basilfx/TRADFRI-Hacking/products/ICPSLC24-10NA/README.md

# ICPSLC24-10NA
LED output controller/dimmer

## Details

* Potted: no

The output appears to be measured by the module somehow.

## Teardown

* [Images](images)
* [Schematics](schematics)

## Pinout

### Module (unverified)
* PA0: K1 (Reset key)
* PA1: Goes to ZD1, through R9 and then to OUT+, possibly output measuring?
* PB13: Pulls down the FET Gate
* PF0: Pin 2 on header
* PF1: Pin 3 on header
