basilfx/TRADFRI-Hacking/products/LED1536G5/README.md

# LED1536G5
TRÅDFRI bulb E12/E14, white spectrum, globe, opal, 400 lm.

## Details

* Socket: E14
* Potted: likely
