basilfx/TRADFRI-Hacking/products/LED1537R6/README.md

# LED1537R6
TRÅDFRI bulb GU10, white spectrum, 400 lm.

## Details

* Socket: GU10
* Potted: yes

## Teardown
The potting material can be easily removed. It does not stick and will crumble
in smaller peaces once you remove it.

* [Images](images)

## Pinouts
* 1: Common (+ max 28.4V @ 100%)
* 2: Warm leds (-)
* 3: Cold leds (-)
