basilfx/TRADFRI-Hacking/products/LED1545G12/README.md

# LED1545G12
TRÅDFRI bulb E26/E27, white spectrum, globe, opal, 980 lm.

## Details:

* Socket: E27
* Potted: likely
