basilfx/TRADFRI-Hacking/products/LED1546G12/README.md

# LED1546G12
TRADFRI bulb E26/E27, white spectrum, globe, clear, 950 lm.

## Details

* Socket: E27
* Potted: likely
