basilfx/TRADFRI-Hacking/products/LED1622G12/README.md

# LED1622G12
TRÅDFRI bulb E26, white, globe, opal, 1000 lm.

## Details

* Socket: E27
* Potted: likely
