basilfx/TRADFRI-Hacking/products/LED1623G12/README.md

# LED1623G12
TRÅDFRI bulb E27, white, globe, opal, 1000 lm.

## Details

* Socket: E27
* Potted: likely
