basilfx/TRADFRI-Hacking/products/LED1624G9/README.md

# LED1624G9
TRÅDFRI bulb E12/E14/E26/E27, color/white spectum, globe, opal, 600 lm.

## Details

* Socket: E27
* Potted: likely
