basilfx/TRADFRI-Hacking/products/LED1650R5/README.md

# LED1650R5
TRÅDFRI bulb GU10, white, 400 lm

## Details

* Socket: GU10
* Potted: no
* TRÅDFRI Module: ICC-1

## Teardown
Use a small flat screw driver to lift up the plastic lens.

* [Images](products/LED1650R5/images)

## Pinout

### Module

* PA1 -> unused (but soldered)
* PB13 -> LED driver

## Power consumption
Measured using a Voltcraft 3000 energy monitor.

| Brightness | Power (W) | Cos φ |
|---|---|---|
| 100% | 6.0 | 0.80  |
| 50% | 1.6 | 0.62  |
| 10% | 0.7 | 0.40  |
| Off | 0.0 | 1.00  |
