basilfx/TRADFRI-Hacking/contrib/pcbs/devboard/README.md

# Devboard
Development board to house an ICC-A or ICC-A-1 TRÅDFRI module.

## Known issues
* This board has a non-optimal design for wireless usage. However, the main
  goal of this board is to provide easier pin access.

## Pictures
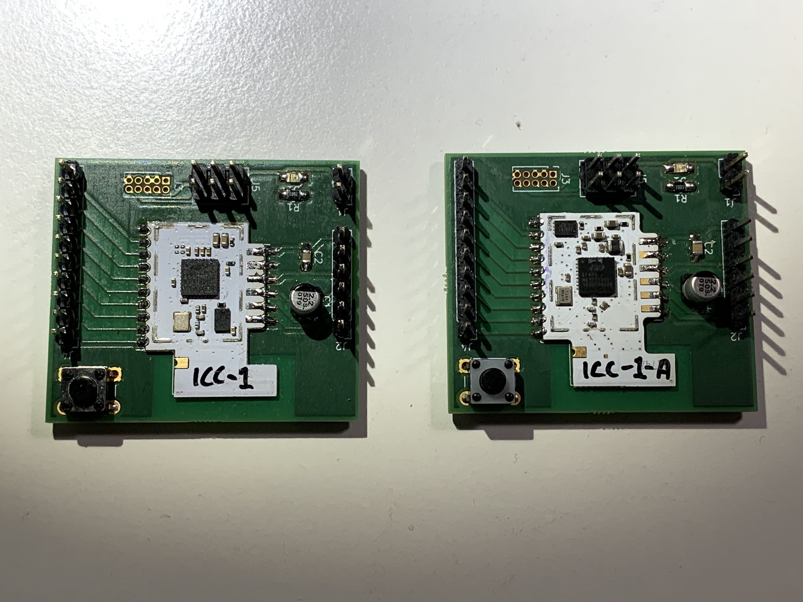
[picture p6: contrib/pcbs/devboard/images/Devboard.jpg]
Assembled board
[](images/Devboard.jpg)

## Board
Top layer
Bottom layer

## Schema
You can find the schema [here](Devboard.pdf).
