basilfx/TRADFRI-Hacking/contrib/pcbs/isolator/README.md

# Isolator
Tiny board to isolate UART RX/TX from target board.

## Pictures
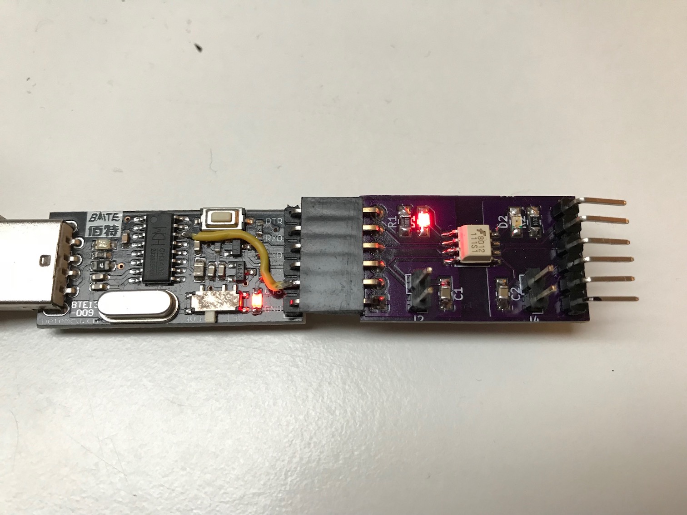
[picture p7: contrib/pcbs/isolator/images/Isolator.jpg]
Assembled board
[](images/Isolator.jpg)

## Board
Top layer
Bottom layer

## Schema
You can find the schema [here](Isolator.pdf).
