basilfx/TRADFRI-Hacking/firmwares/riot-os/spi_flash_dump/README.md

# SPI Flash Dump
Pre-compiled firmware to dump the contents of the SPI NOR Flash chip.

## Source
https://github.com/basilfx/RIOT-applications/tree/master/spi_flash_dump

## Compilation
Ensure that you have a copy of RIOT-OS cloned. 

To compile, run `RIOTBASE=path/to/riot-os BOARD=ikea-tradfri make`.
