basilfx/TRADFRI-Hacking/firmwares/riot-os/default/README.md

# Default
Pre-compiled firmware of RIOT-OS' default application

## Source
https://github.com/RIOT-OS/RIOT/tree/master/examples/default

## Compilation
Ensure that you have a copy of RIOT-OS cloned. 

To compile, run `RIOTBASE=path/to/riot-os BOARD=ikea-tradfri make`.
