basilfx/TRADFRI-Hacking/firmwares/riot-os/spi_flash_identify/README.md

# SPI Flash Identify
Pre-compiled firmware to identify the SPI NOR Flash chip.

## Source
https://github.com/basilfx/RIOT-applications/tree/master/spi_flash_identify

## Compilation
Ensure that you have a copy of RIOT-OS cloned. 

To compile, run `RIOTBASE=path/to/riot-os BOARD=ikea-tradfri make`.
