basilfx/TRADFRI-Hacking/docs/firmware_reversing/images/screenshot_1.png

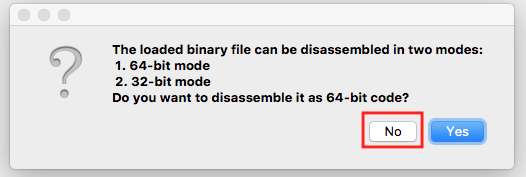
docs/firmware_reversing/images/screenshot_1.png
