basilfx/TRADFRI-Hacking/docs/firmware_reversing/images/screenshot_2.png

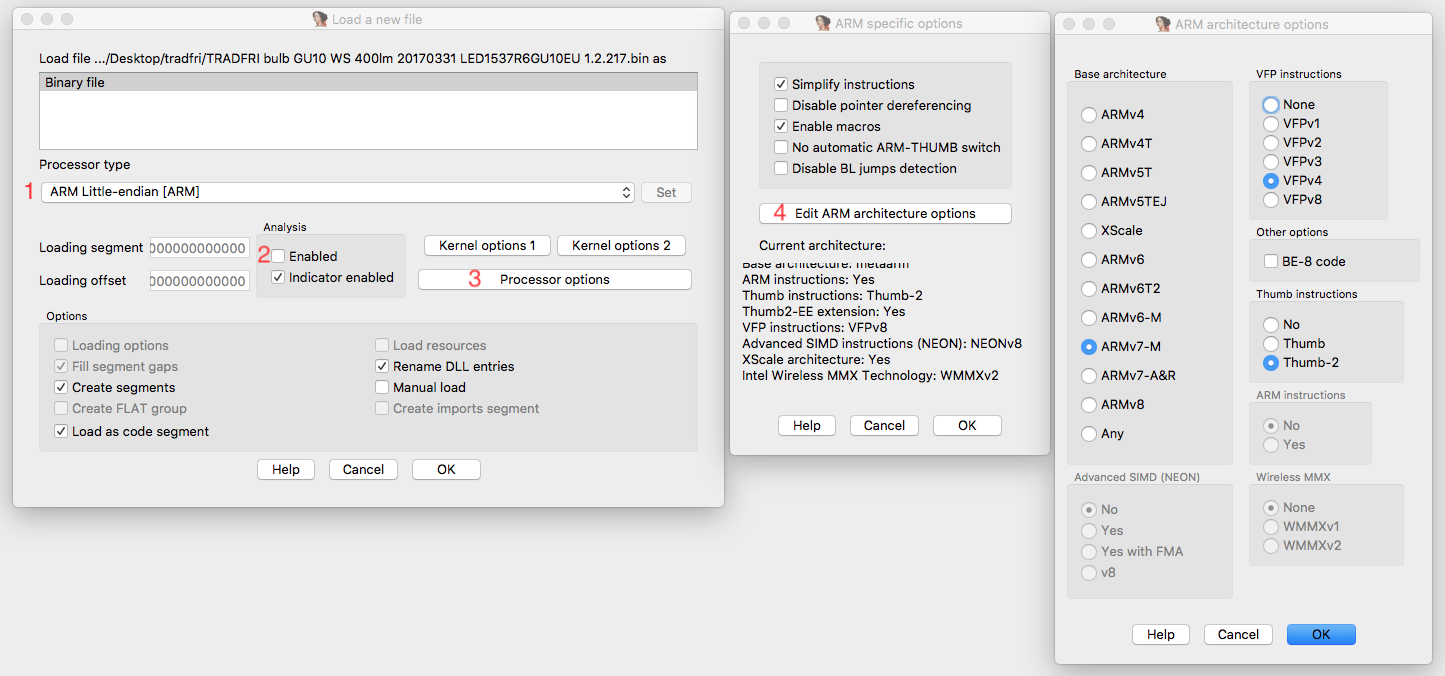
docs/firmware_reversing/images/screenshot_2.png
