basilfx/TRADFRI-Hacking/docs/firmware_reversing/images/screenshot_3.png

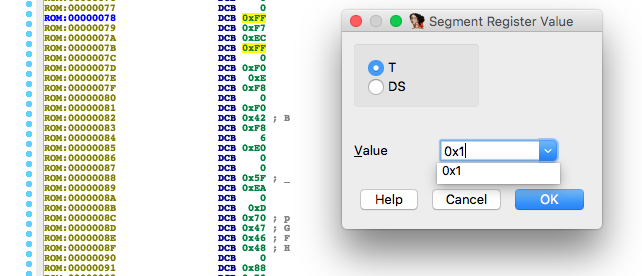
docs/firmware_reversing/images/screenshot_3.png
