basilfx/TRADFRI-Hacking/docs/firmware_reversing/images/screenshot_5.png

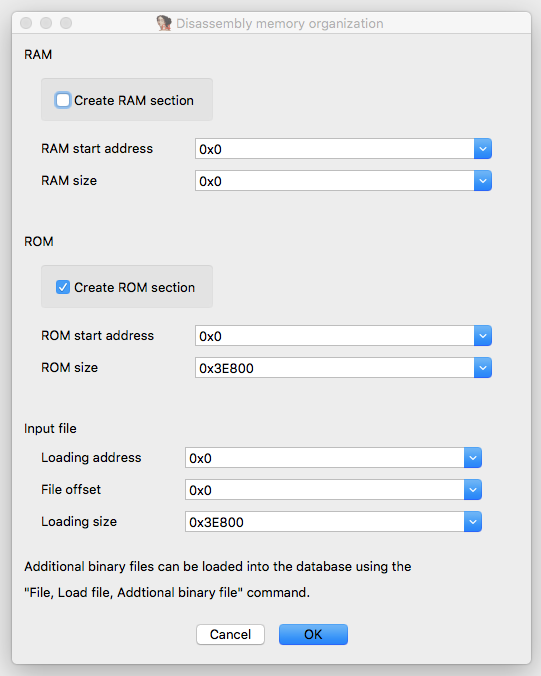
docs/firmware_reversing/images/screenshot_5.png
