basilfx/TRADFRI-Hacking/docs/working_safely/images/led.jpg

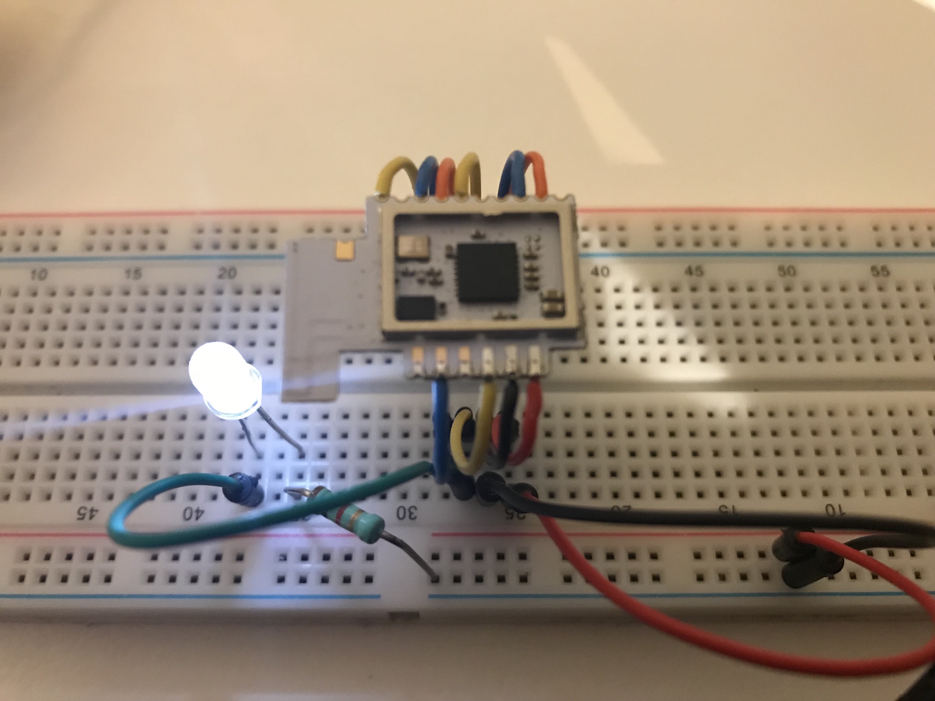
docs/working_safely/images/led.jpg
