basilfx/TRADFRI-Hacking/products/E1526/images/case.jpg

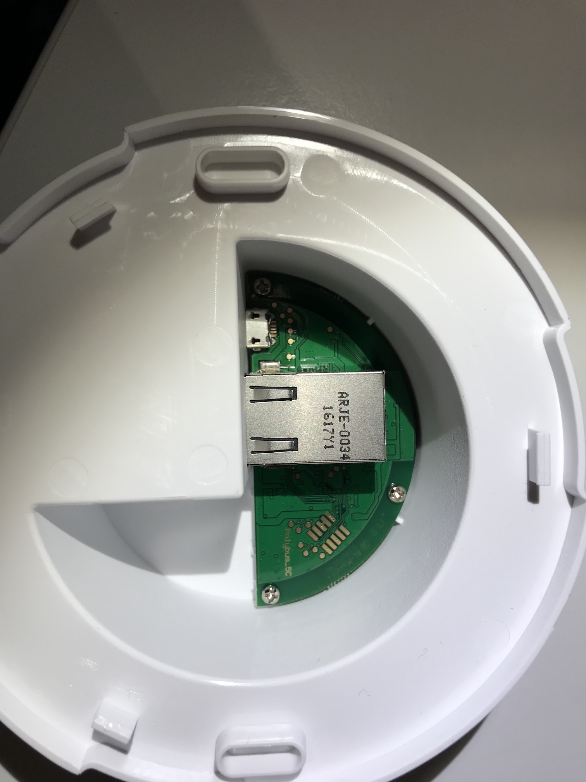
products/E1526/images/case.jpg
