basilfx/TRADFRI-Hacking/products/E1526/images/pcb.jpg

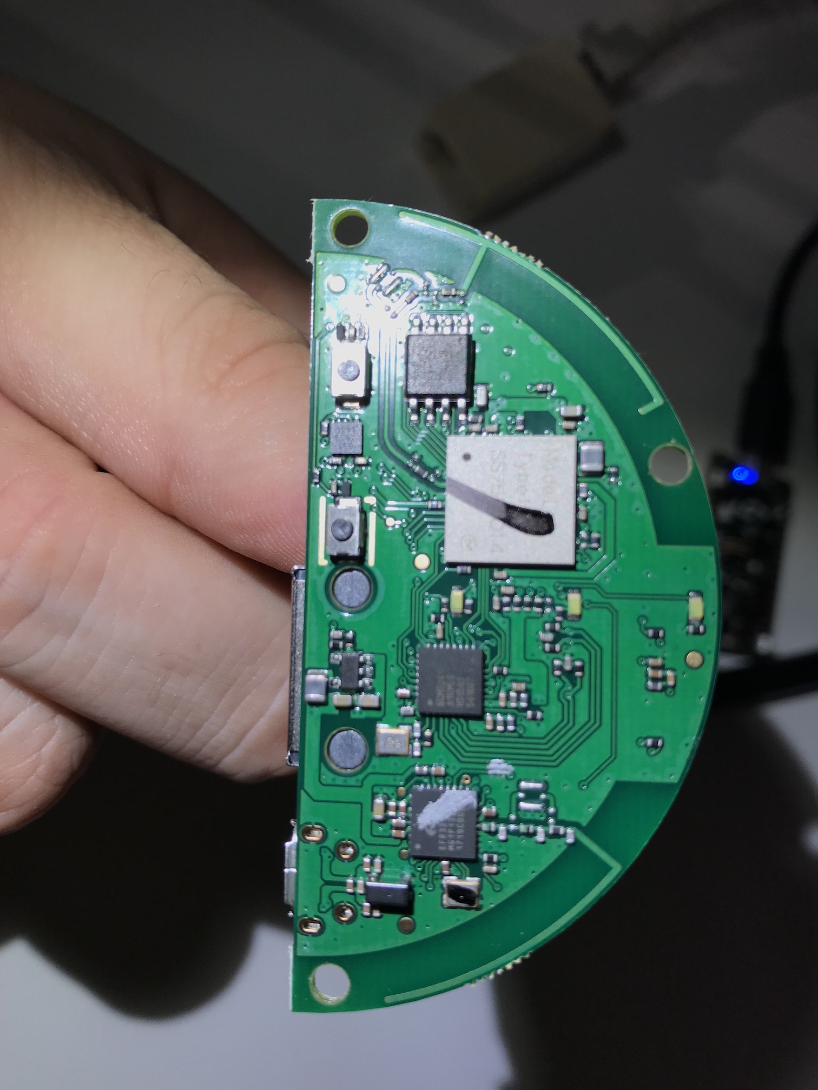
products/E1526/images/pcb.jpg
