basilfx/TRADFRI-Hacking/products/E1745/images/back.jpg

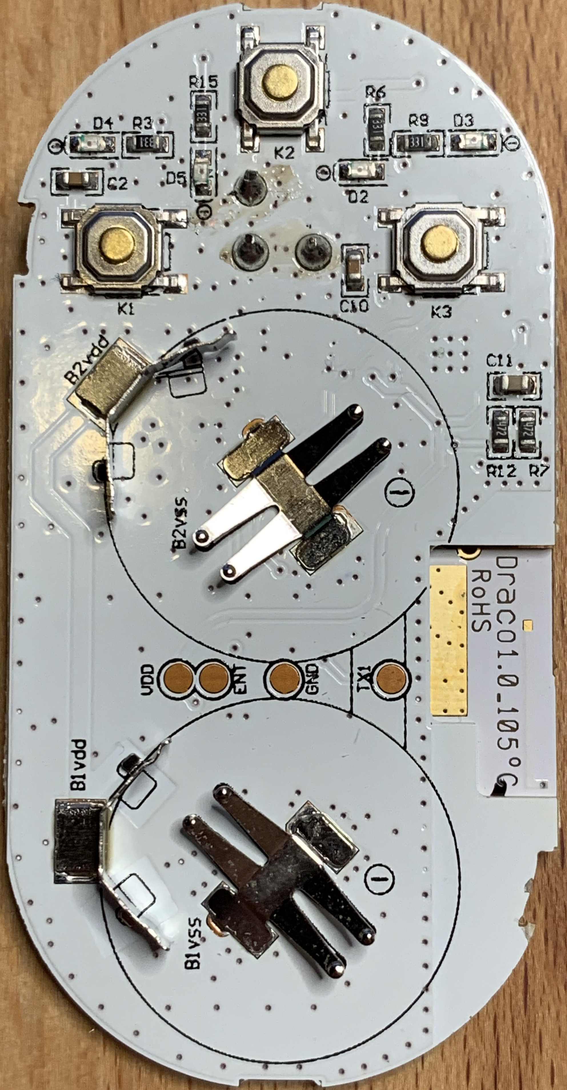
products/E1745/images/back.jpg
