basilfx/TRADFRI-Hacking/products/E1745/images/front.jpg

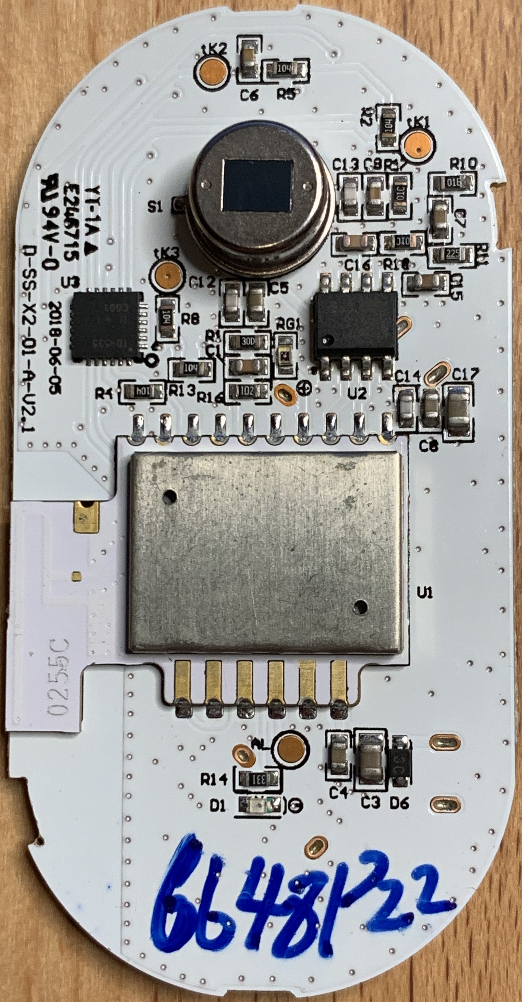
products/E1745/images/front.jpg
