basilfx/TRADFRI-Hacking/products/E1812/images/back.jpg

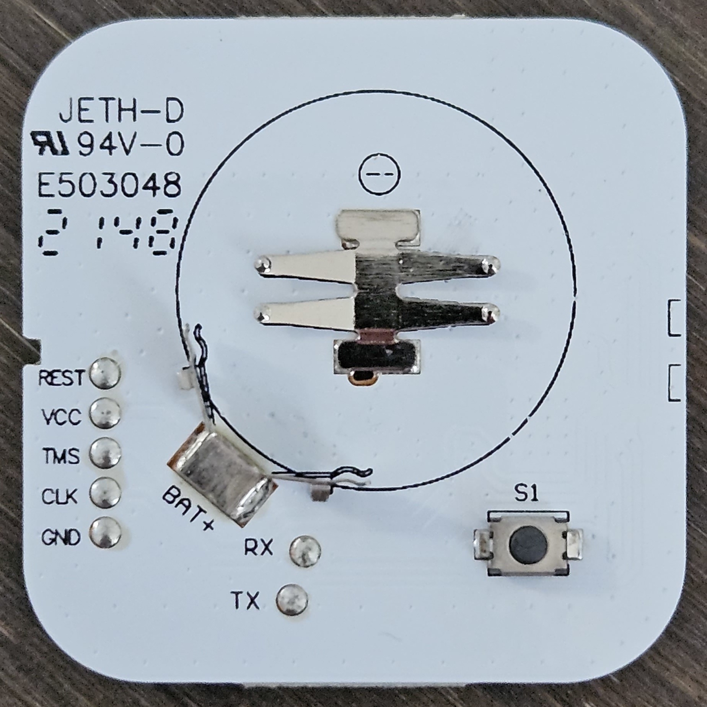
products/E1812/images/back.jpg
