basilfx/TRADFRI-Hacking/products/E1812/images/front.jpg

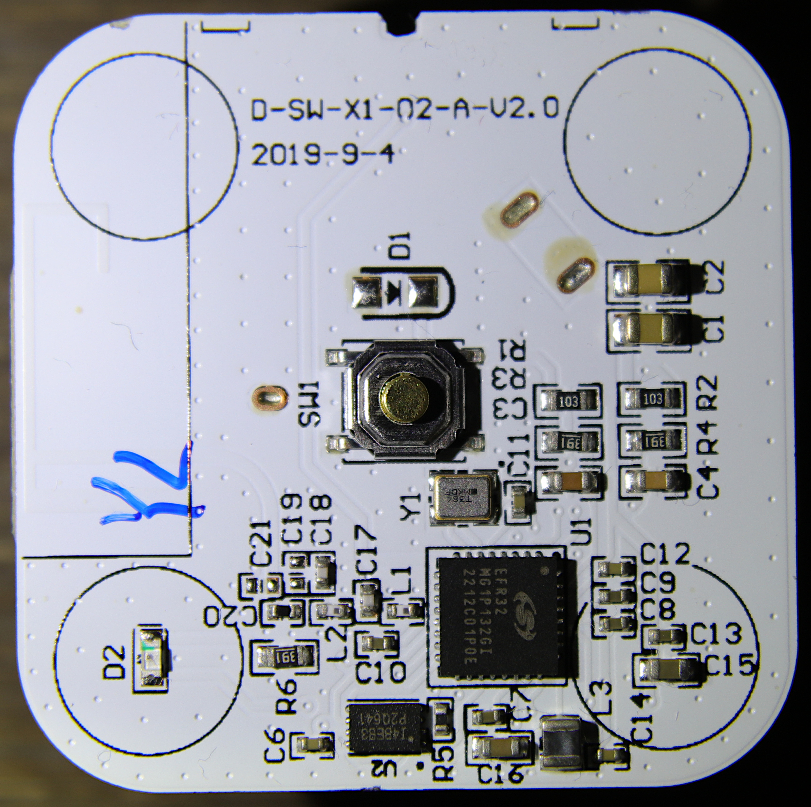
products/E1812/images/front.jpg
