basilfx/TRADFRI-Hacking/products/E1836/images/IMG_1090.jpeg

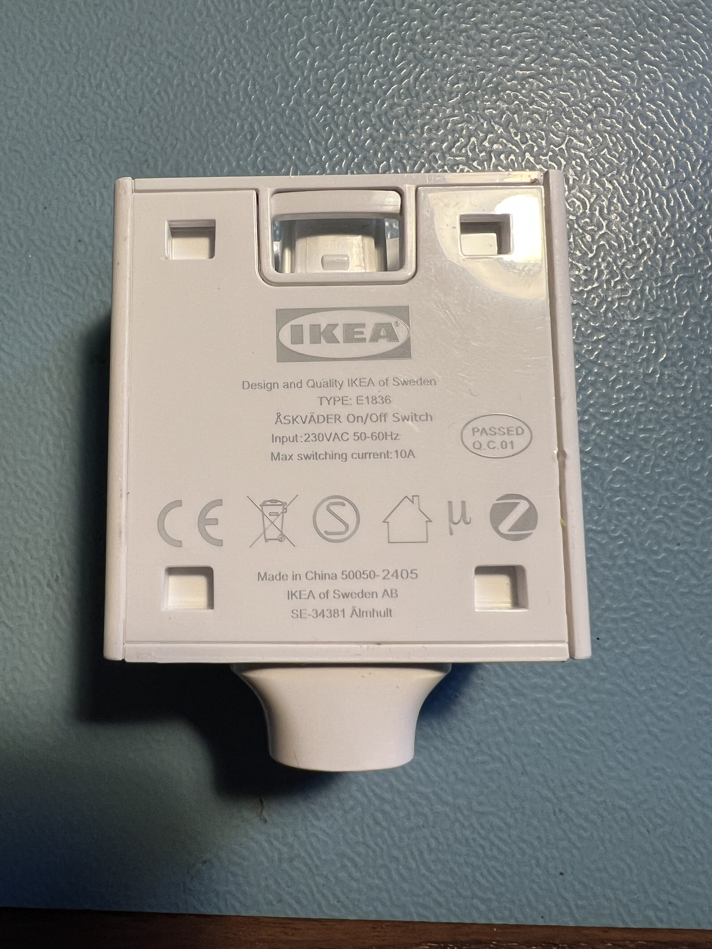
products/E1836/images/IMG_1090.jpeg
