basilfx/TRADFRI-Hacking/products/E1836/images/IMG_1091.jpeg

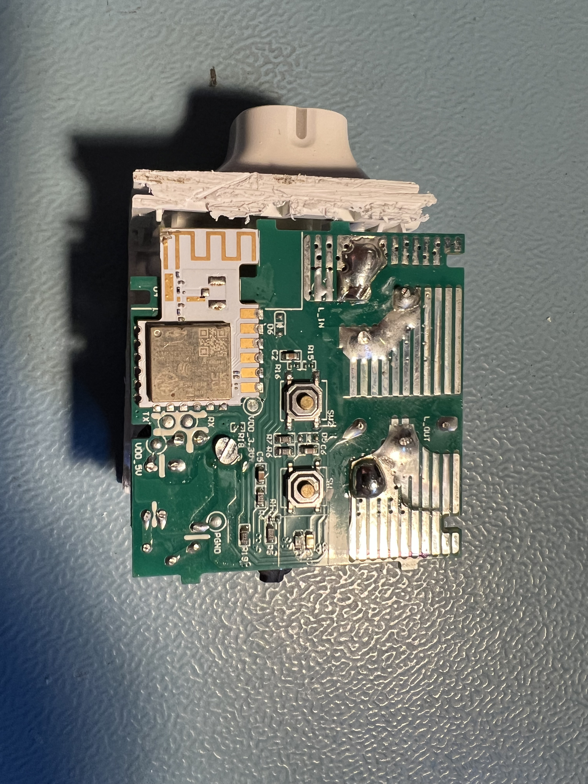
products/E1836/images/IMG_1091.jpeg
