basilfx/TRADFRI-Hacking/products/E1836/images/IMG_1092.jpeg

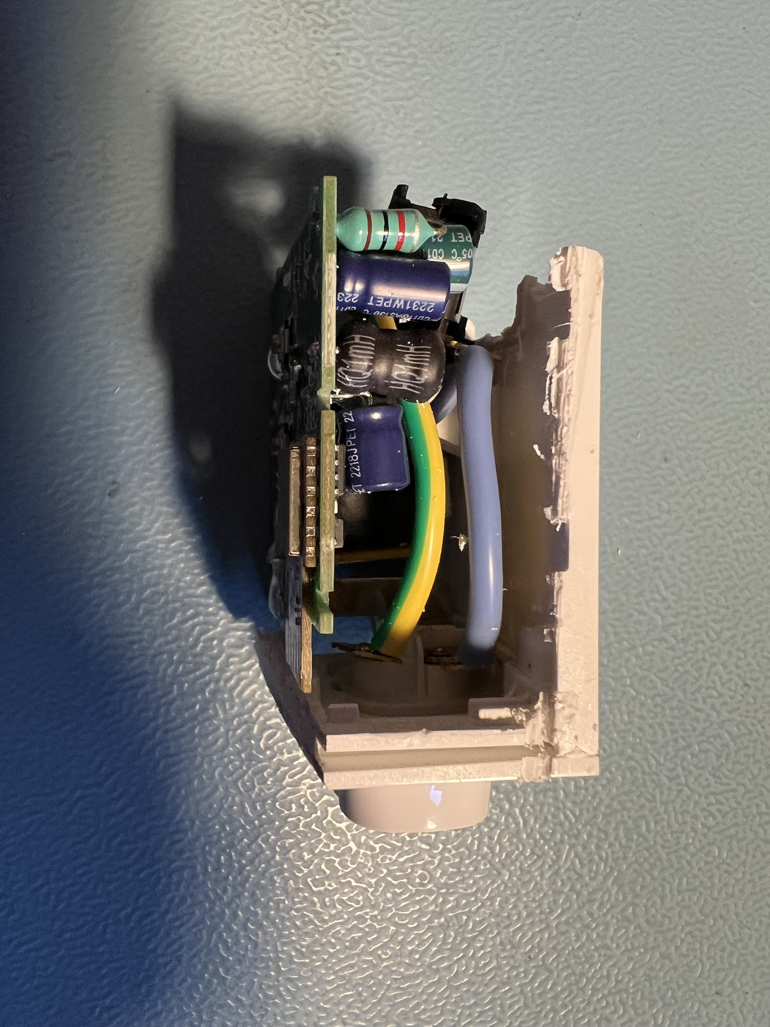
products/E1836/images/IMG_1092.jpeg
