basilfx/TRADFRI-Hacking/products/E1836/images/IMG_1093.jpeg

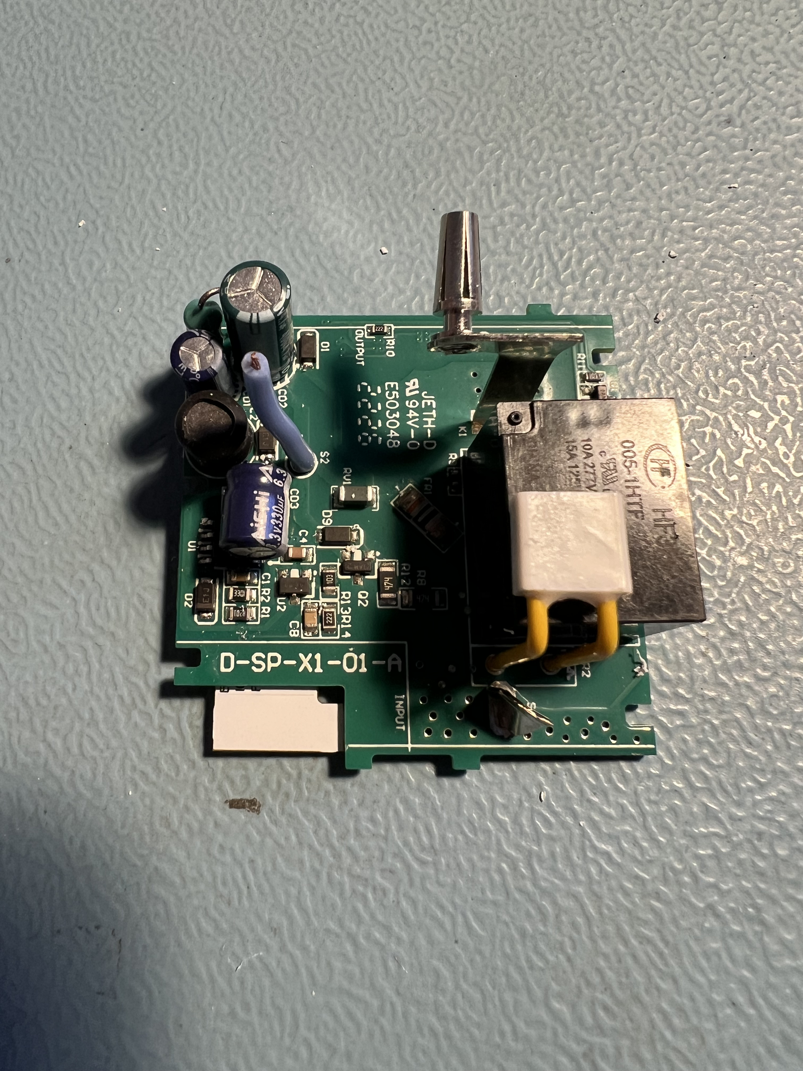
products/E1836/images/IMG_1093.jpeg
