basilfx/TRADFRI-Hacking/products/E2013/images/pcb-back.jpg

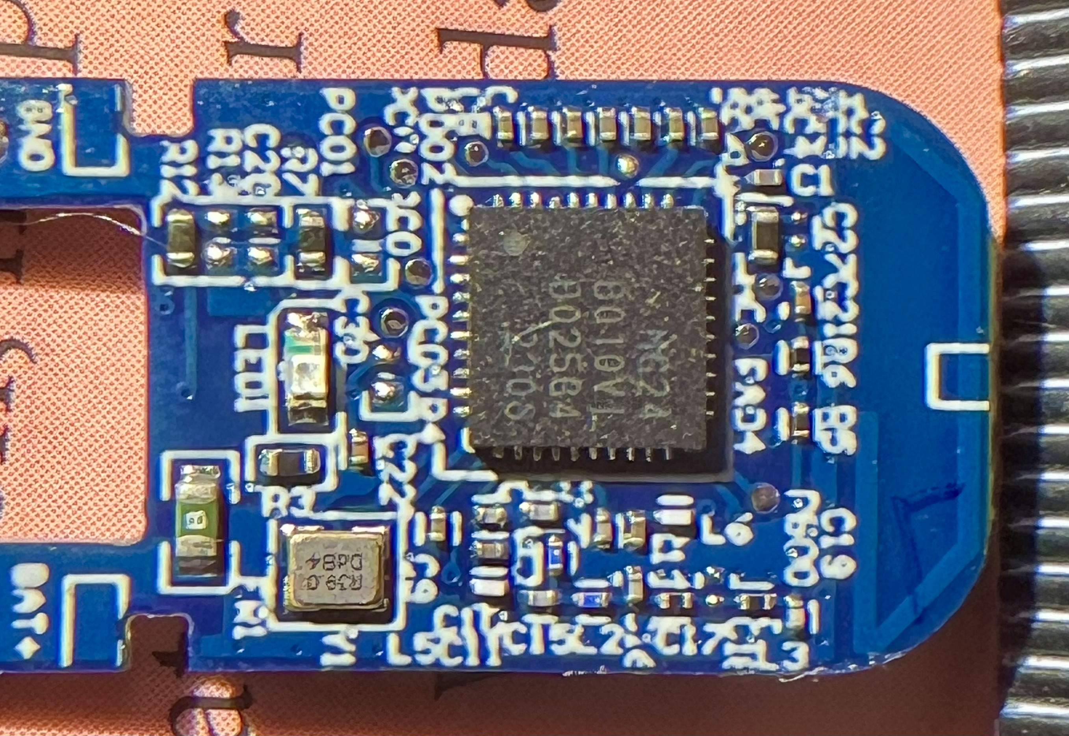
products/E2013/images/pcb-back.jpg
