basilfx/TRADFRI-Hacking/products/E2013/images/pcb-stripped-back.jpg

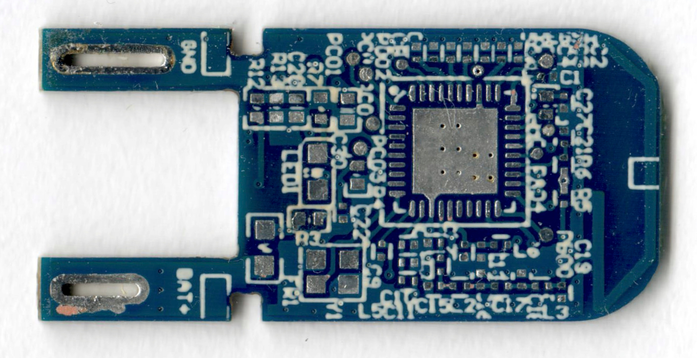
products/E2013/images/pcb-stripped-back.jpg
