basilfx/TRADFRI-Hacking/products/E2013/images/pcb-stripped-front.jpg

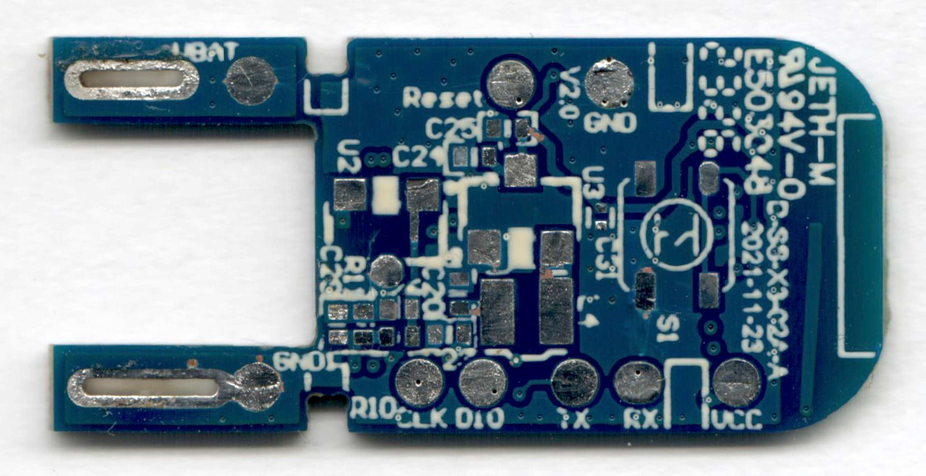
products/E2013/images/pcb-stripped-front.jpg
