basilfx/TRADFRI-Hacking/products/E2013/images/pcb-traces-back.jpg

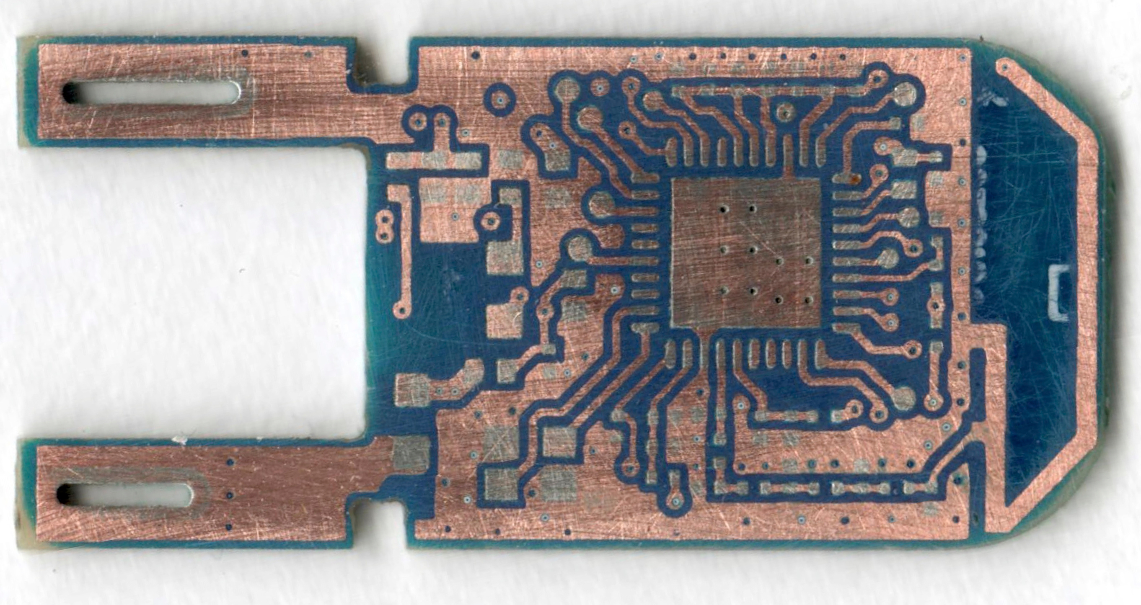
products/E2013/images/pcb-traces-back.jpg
