basilfx/TRADFRI-Hacking/products/E2013/images/pcb-traces-front.jpg

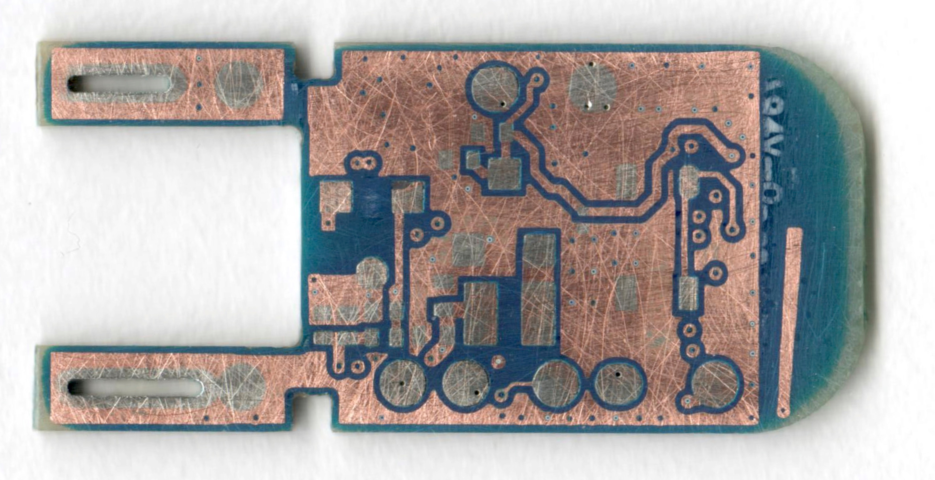
products/E2013/images/pcb-traces-front.jpg
