basilfx/TRADFRI-Hacking/products/E2123/images/case_bot.jpg

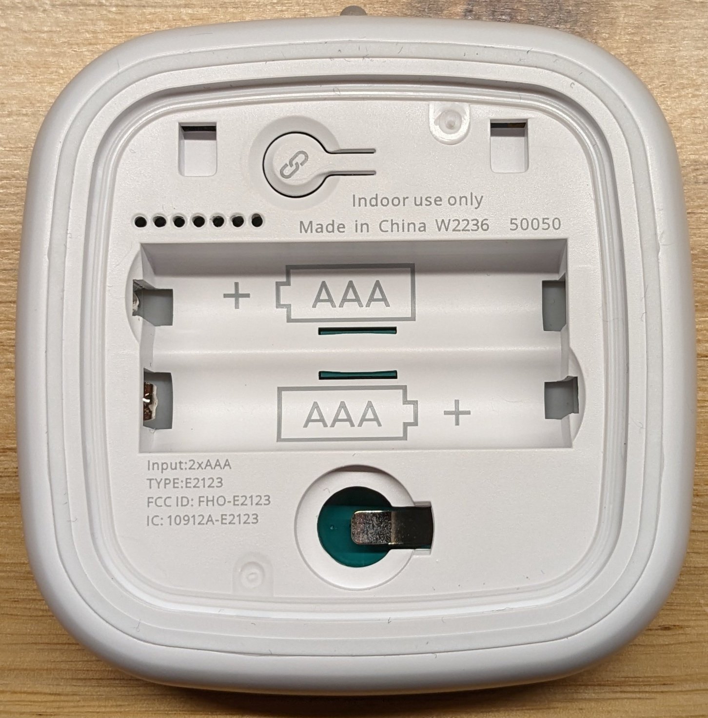
products/E2123/images/case_bot.jpg
