basilfx/TRADFRI-Hacking/products/E2123/images/pcb_bot.jpg

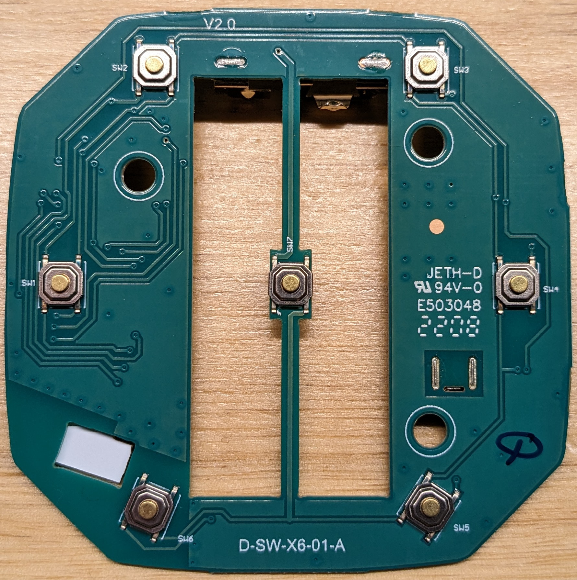
products/E2123/images/pcb_bot.jpg
