basilfx/TRADFRI-Hacking/products/E2123/images/pcb_top.jpg

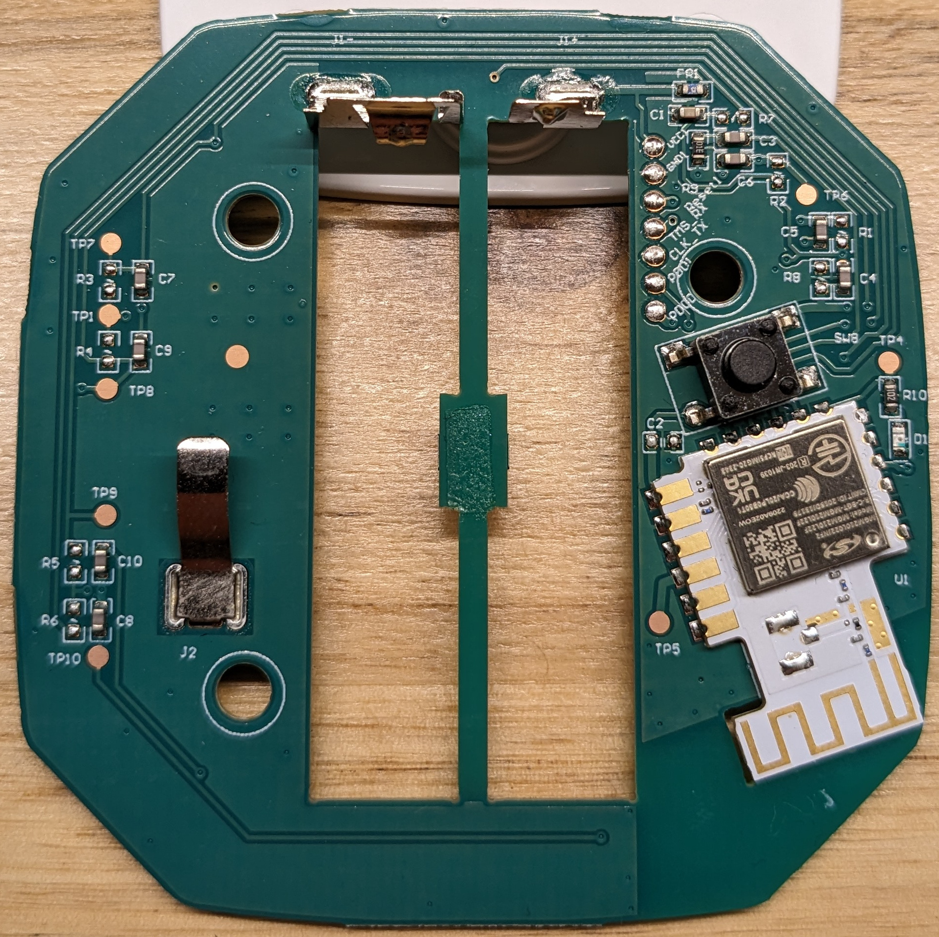
products/E2123/images/pcb_top.jpg
