basilfx/TRADFRI-Hacking/products/E2201/images/case_bot.JPG

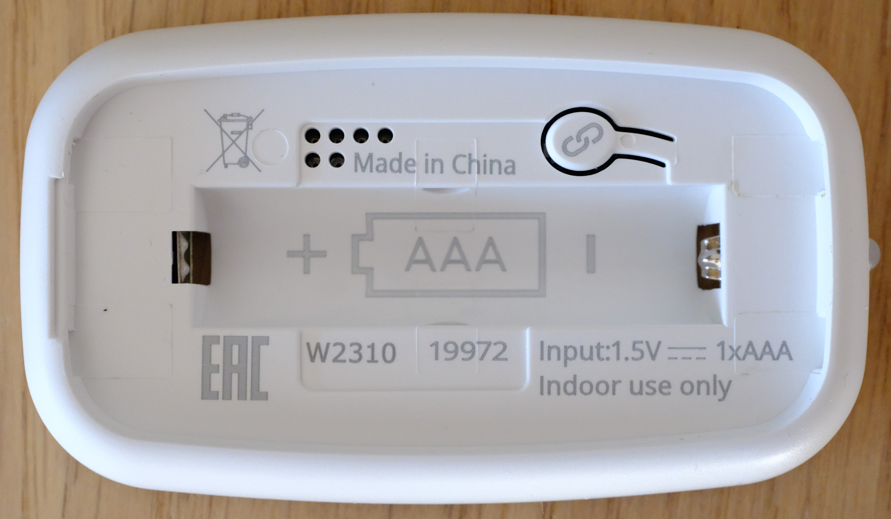
products/E2201/images/case_bot.JPG
