basilfx/TRADFRI-Hacking/products/E2201/images/case_top.JPG

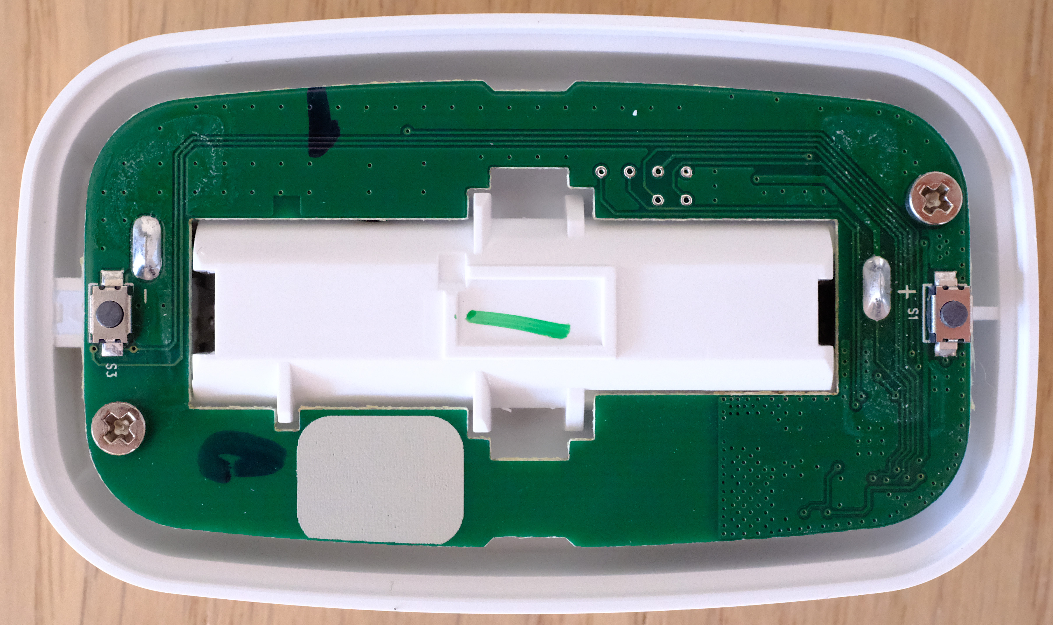
products/E2201/images/case_top.JPG
