basilfx/TRADFRI-Hacking/products/E2201/images/pcb_bot.JPG

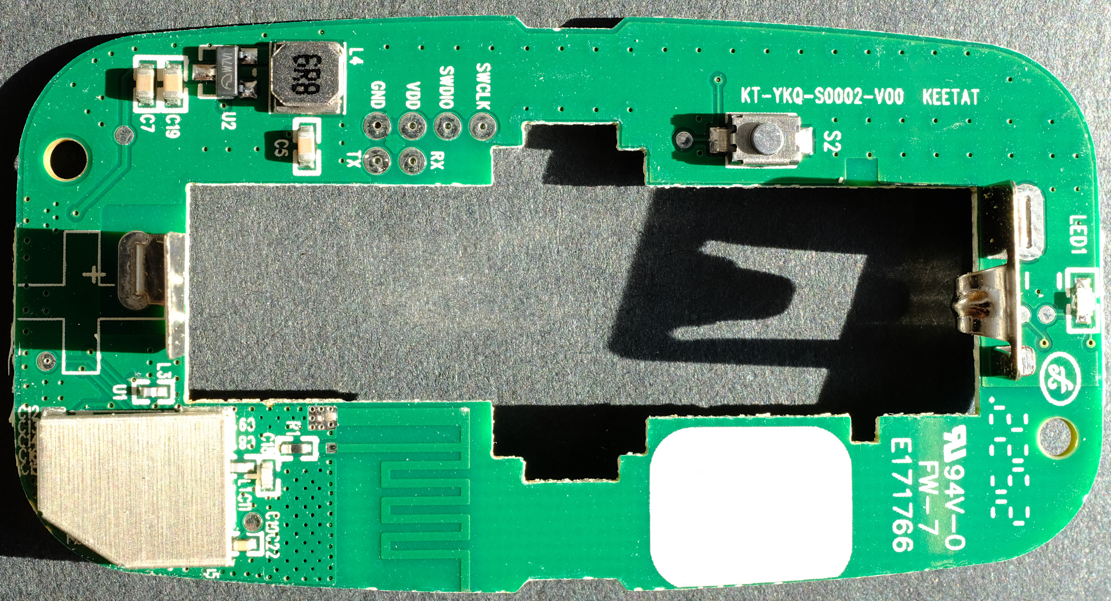
products/E2201/images/pcb_bot.JPG
