basilfx/TRADFRI-Hacking/products/E2201/images/pcb_top.JPG

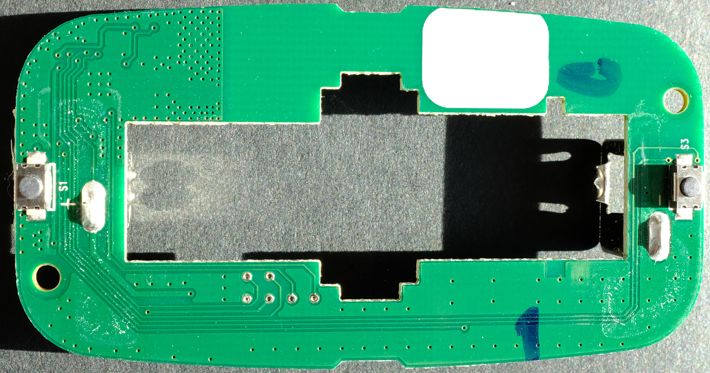
products/E2201/images/pcb_top.JPG
