basilfx/TRADFRI-Hacking/products/E2201/images/shield_can_removed.JPG

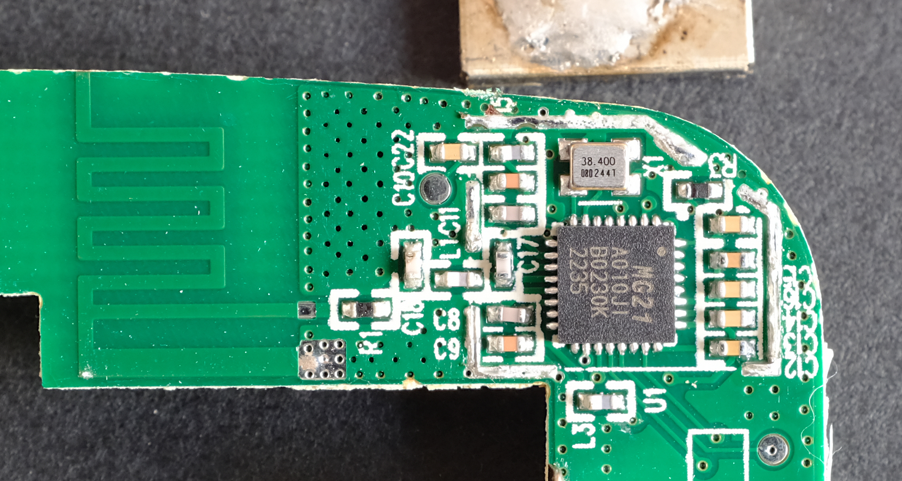
products/E2201/images/shield_can_removed.JPG
