basilfx/TRADFRI-Hacking/products/E2204/images/IMG_0783.jpeg

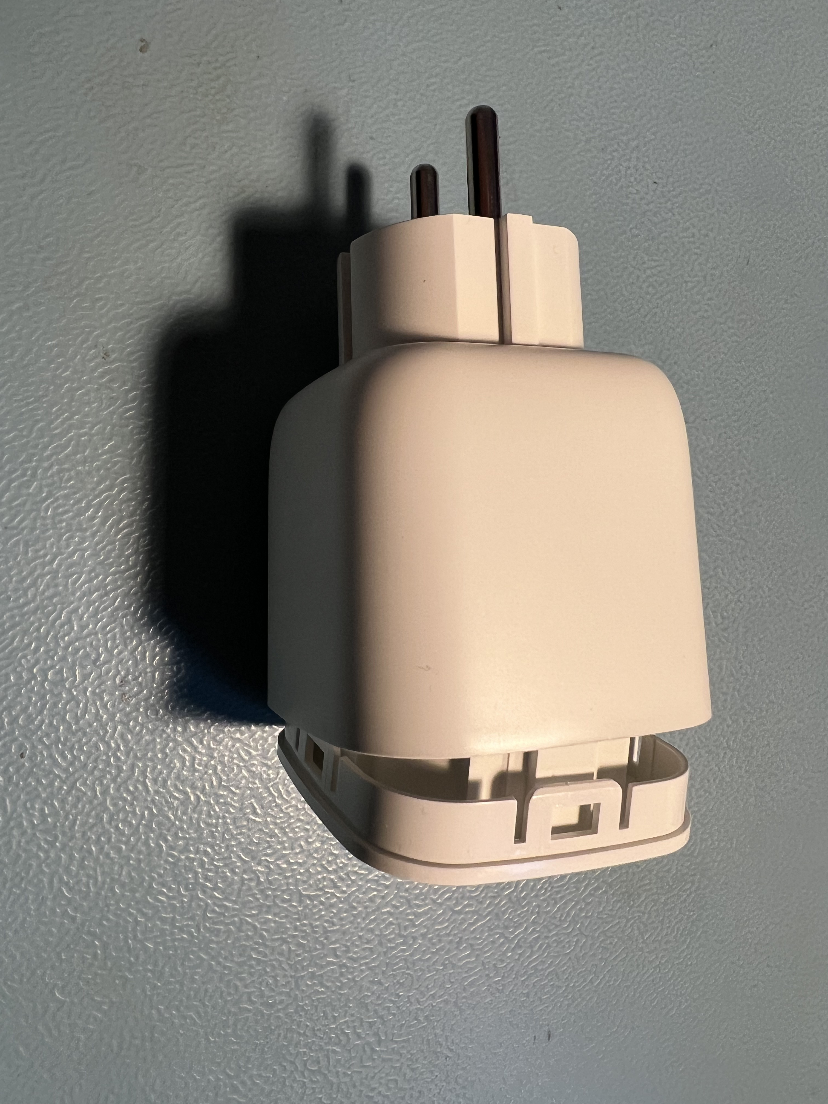
products/E2204/images/IMG_0783.jpeg
