basilfx/TRADFRI-Hacking/products/E2204/images/IMG_0784.jpeg

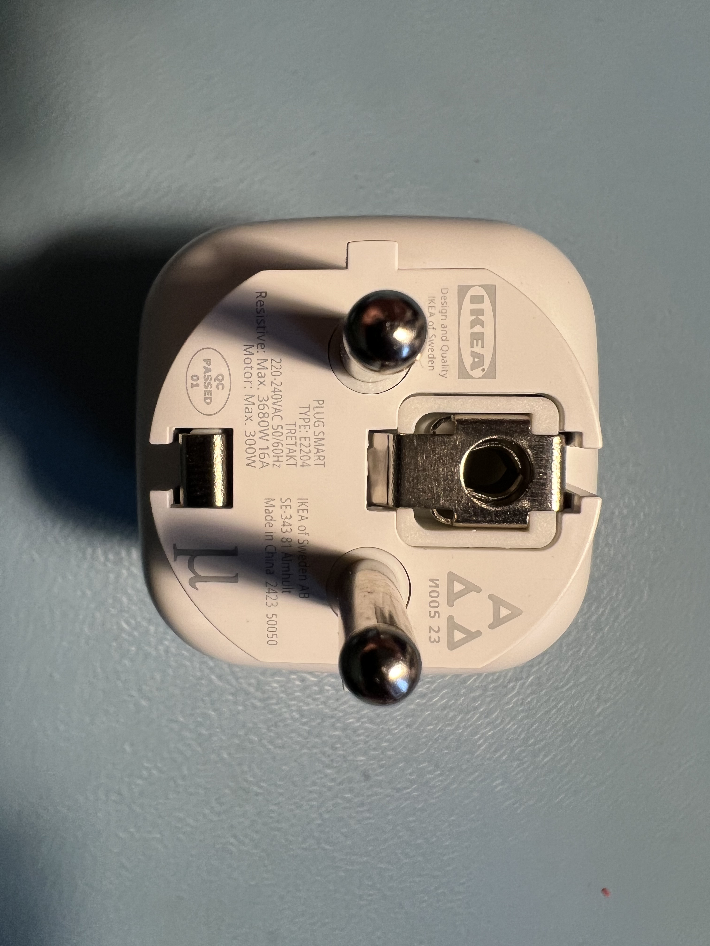
products/E2204/images/IMG_0784.jpeg
