basilfx/TRADFRI-Hacking/products/E2204/images/IMG_0785.jpeg

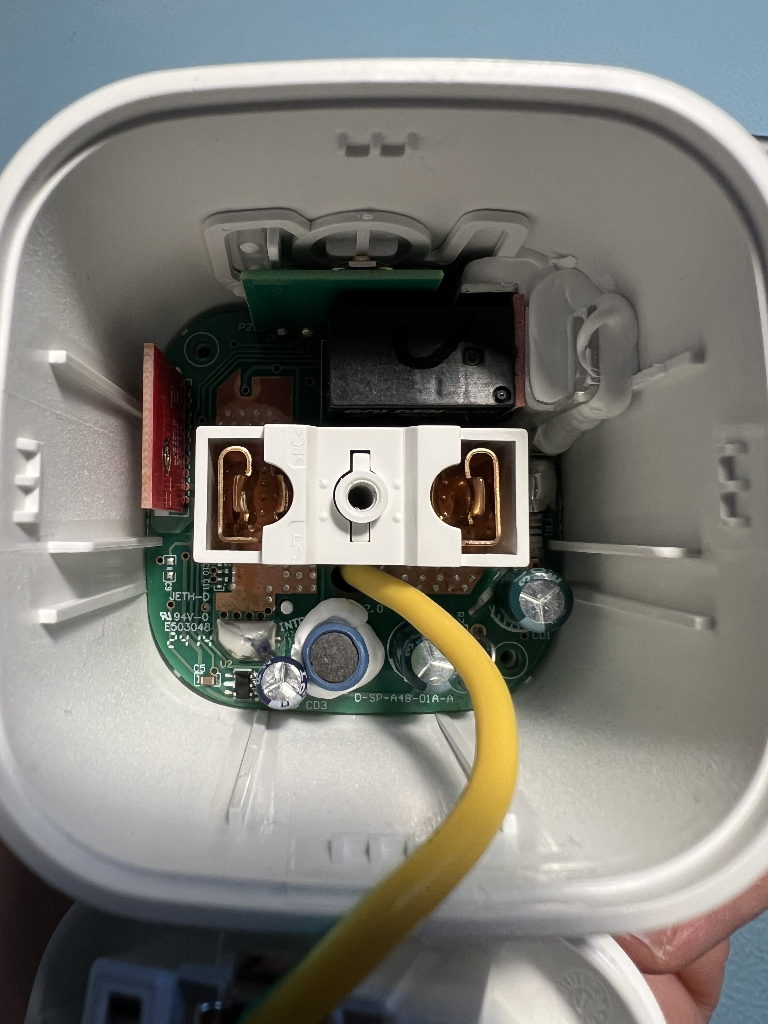
products/E2204/images/IMG_0785.jpeg
