basilfx/TRADFRI-Hacking/products/E2204/images/IMG_0786.jpeg

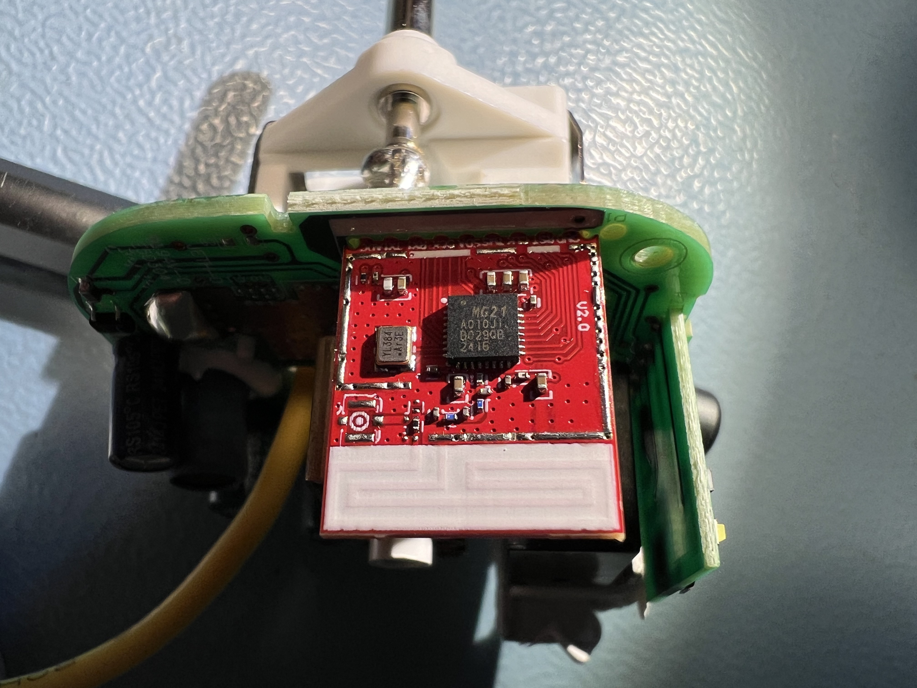
products/E2204/images/IMG_0786.jpeg
