basilfx/TRADFRI-Hacking/products/E2204/images/IMG_0787.jpeg

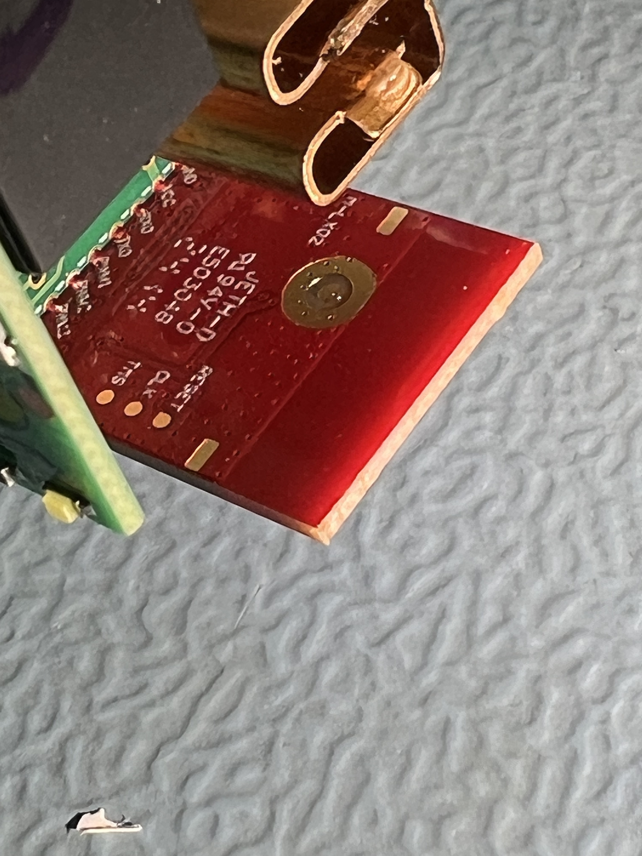
products/E2204/images/IMG_0787.jpeg
