basilfx/TRADFRI-Hacking/products/E2204/images/IMG_0788.jpeg

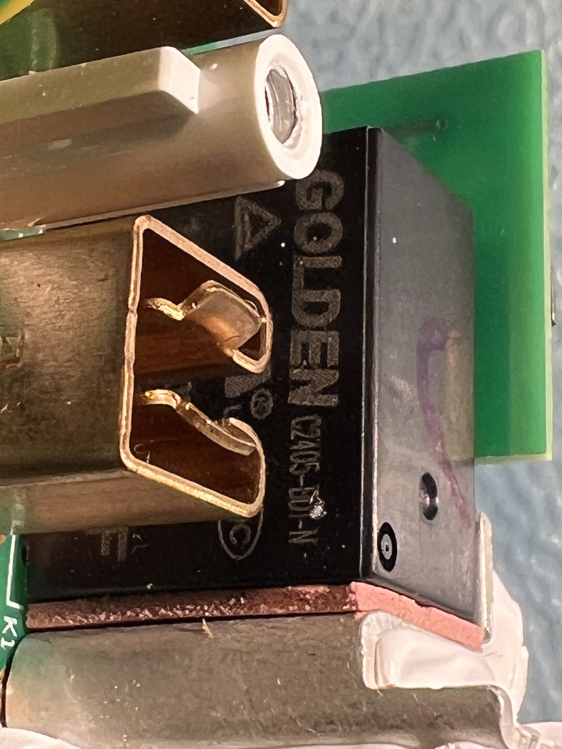
products/E2204/images/IMG_0788.jpeg
