basilfx/TRADFRI-Hacking/products/E2206/images/IMG_1346.jpeg

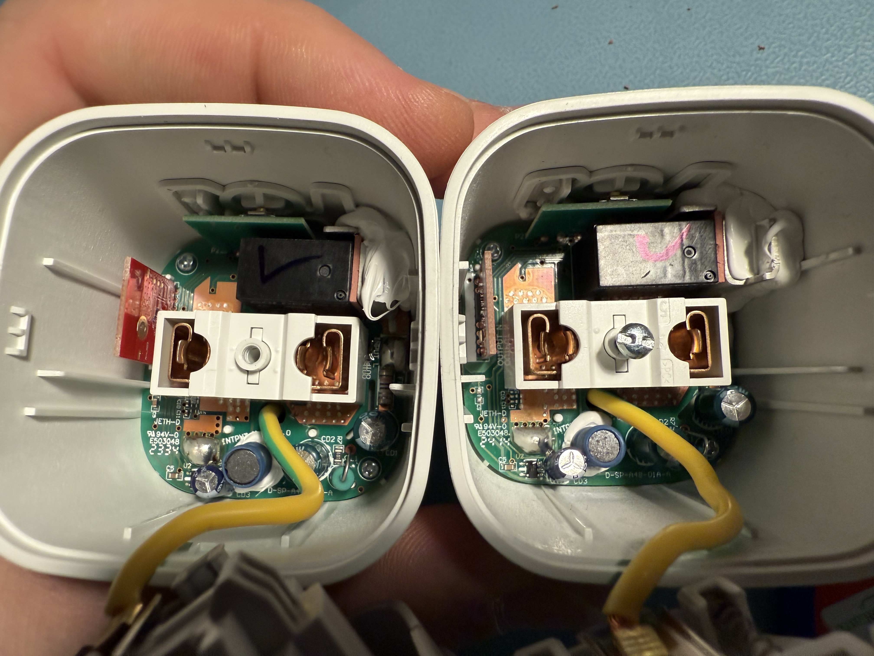
products/E2206/images/IMG_1346.jpeg
