basilfx/TRADFRI-Hacking/products/E2206/images/IMG_1348.jpeg

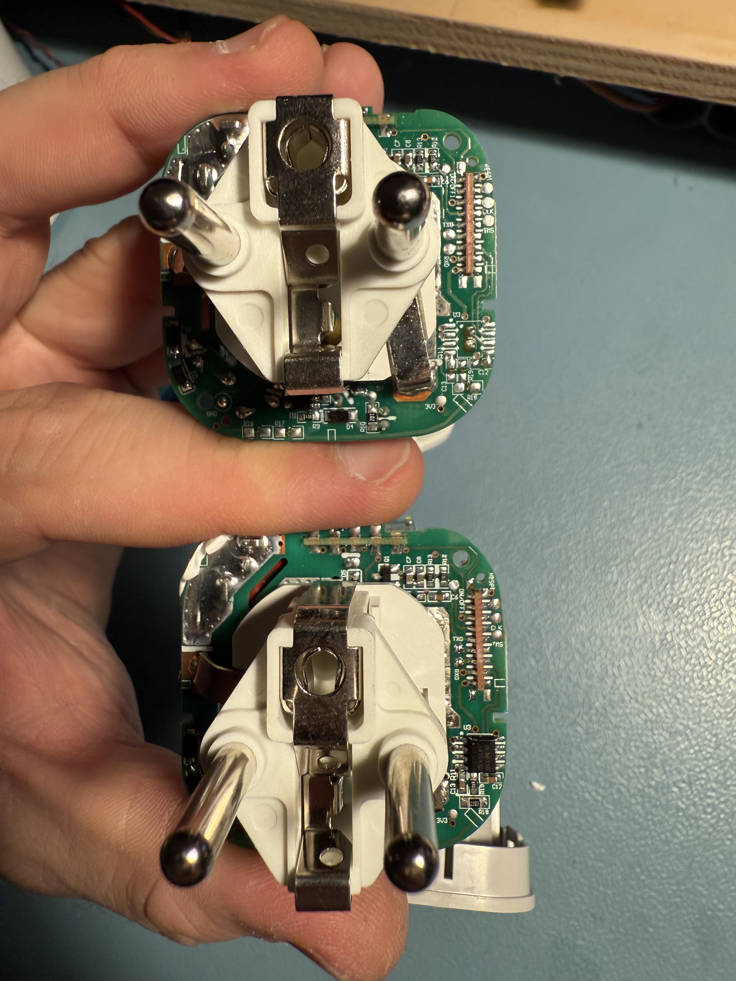
products/E2206/images/IMG_1348.jpeg
