basilfx/TRADFRI-Hacking/products/E2206/images/IMG_1350.jpeg

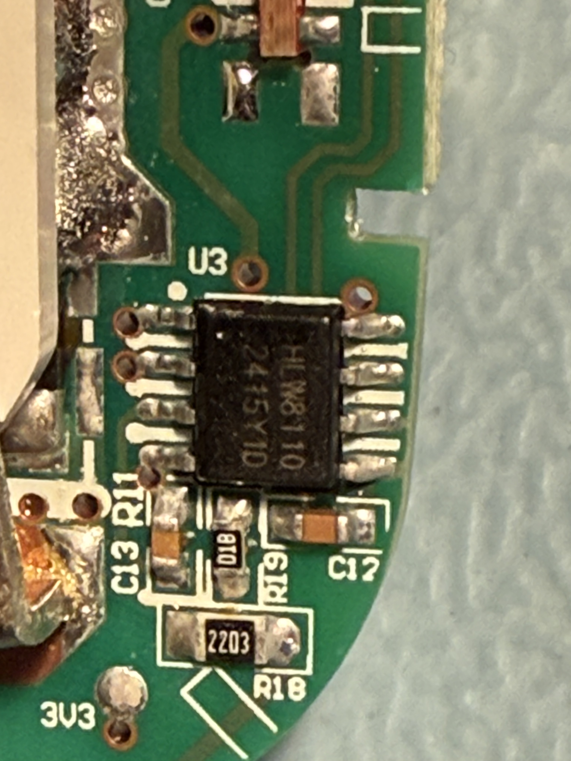
products/E2206/images/IMG_1350.jpeg
