basilfx/TRADFRI-Hacking/products/E2206/images/IMG_1351.jpeg

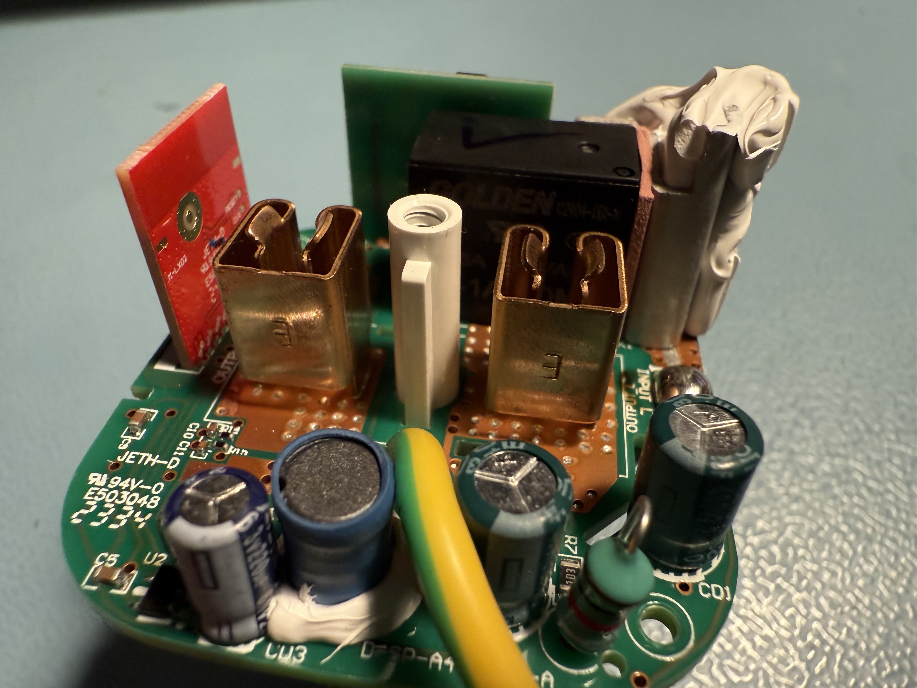
products/E2206/images/IMG_1351.jpeg
