basilfx/TRADFRI-Hacking/products/E2206/images/IMG_1353.jpeg

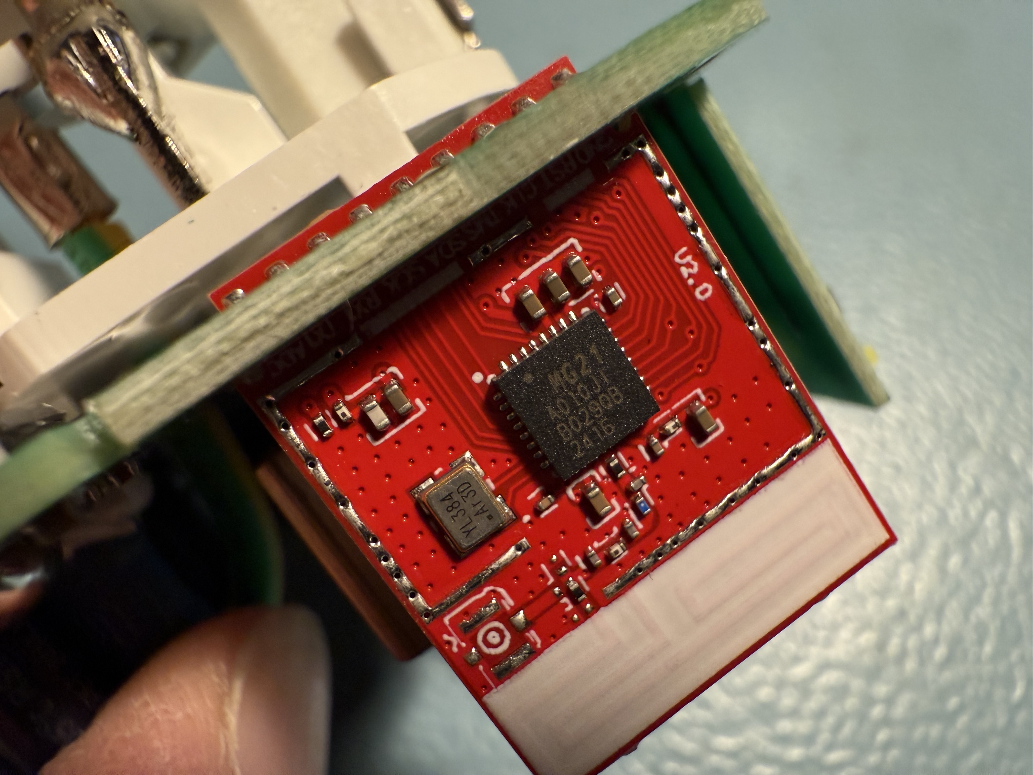
products/E2206/images/IMG_1353.jpeg
