basilfx/TRADFRI-Hacking/products/E2206/images/IMG_1356.jpeg

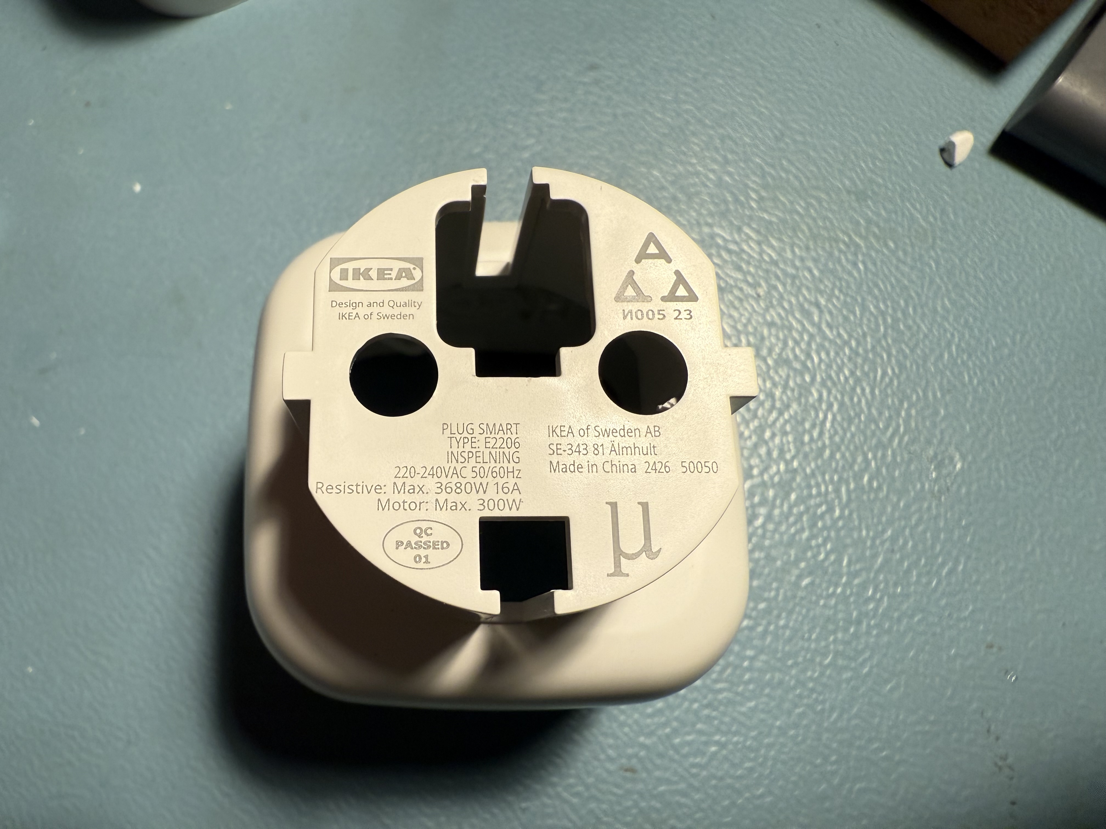
products/E2206/images/IMG_1356.jpeg
