basilfx/TRADFRI-Hacking/products/ICPSHC24-10EU-IL-1/images/closeup_label_01.jpg

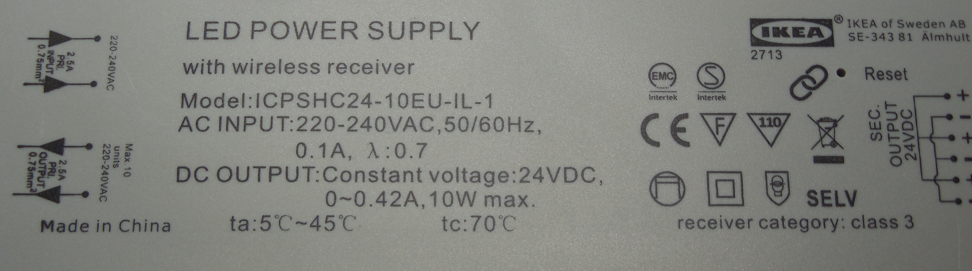
products/ICPSHC24-10EU-IL-1/images/closeup_label_01.jpg
