basilfx/TRADFRI-Hacking/products/ICPSHC24-10EU-IL-1/images/power_control_bottom_01.jpg

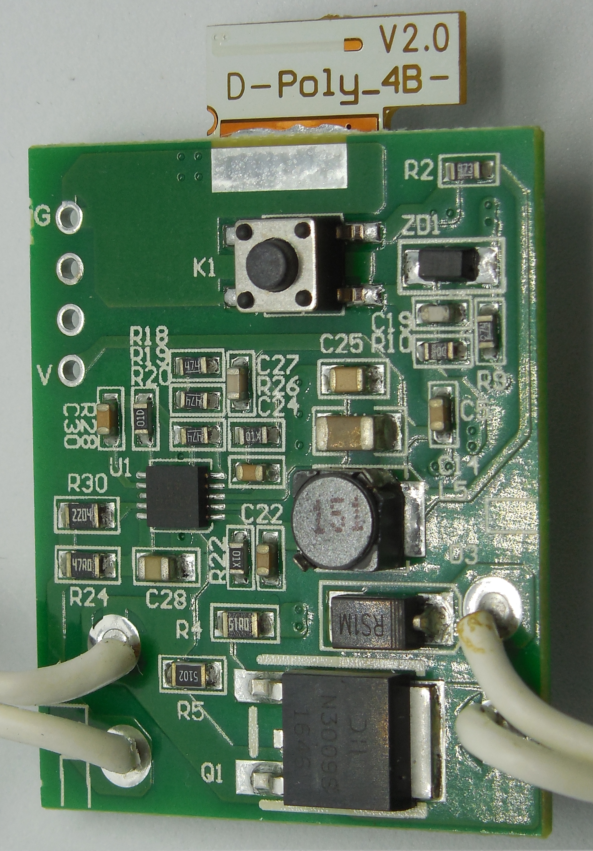
products/ICPSHC24-10EU-IL-1/images/power_control_bottom_01.jpg
