basilfx/TRADFRI-Hacking/products/ICPSHC24-10EU-IL-1/images/power_control_bottom_02.jpg

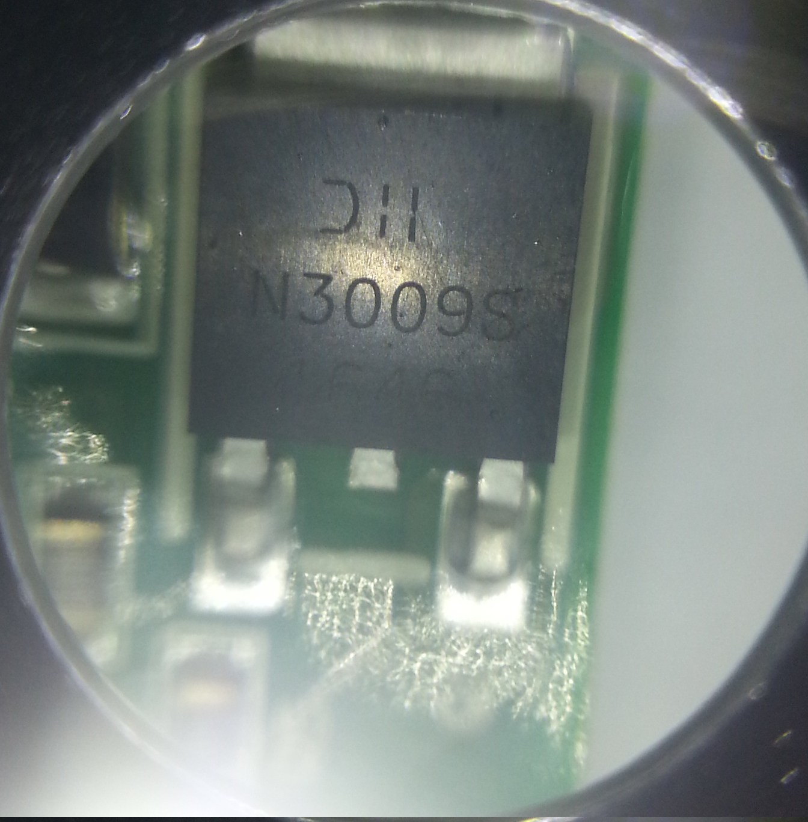
products/ICPSHC24-10EU-IL-1/images/power_control_bottom_02.jpg
