basilfx/TRADFRI-Hacking/products/ICPSHC24-30EU-IL-1/images/module_bottom_01.jpg

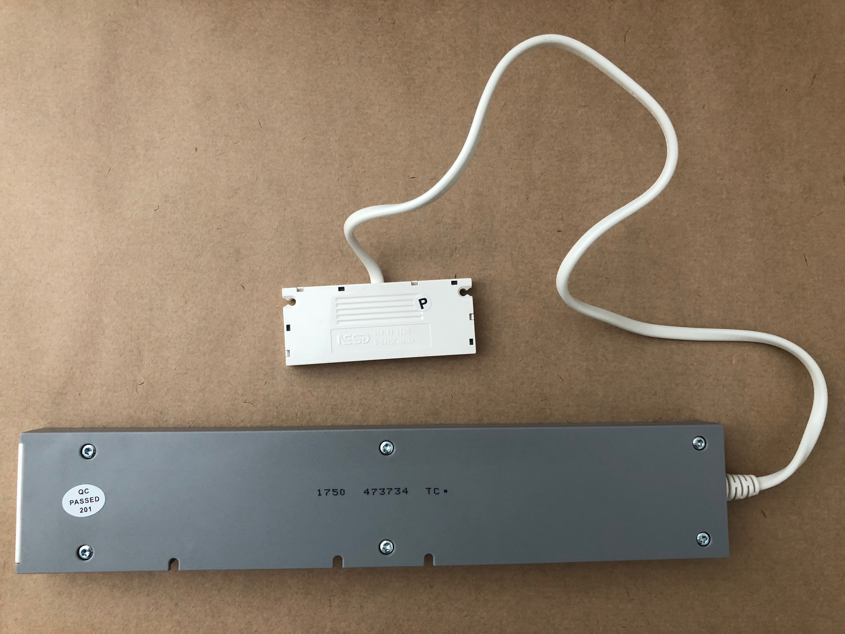
products/ICPSHC24-30EU-IL-1/images/module_bottom_01.jpg
