basilfx/TRADFRI-Hacking/products/ICPSHC24-30EU-IL-1/images/power_control_top_01.jpg

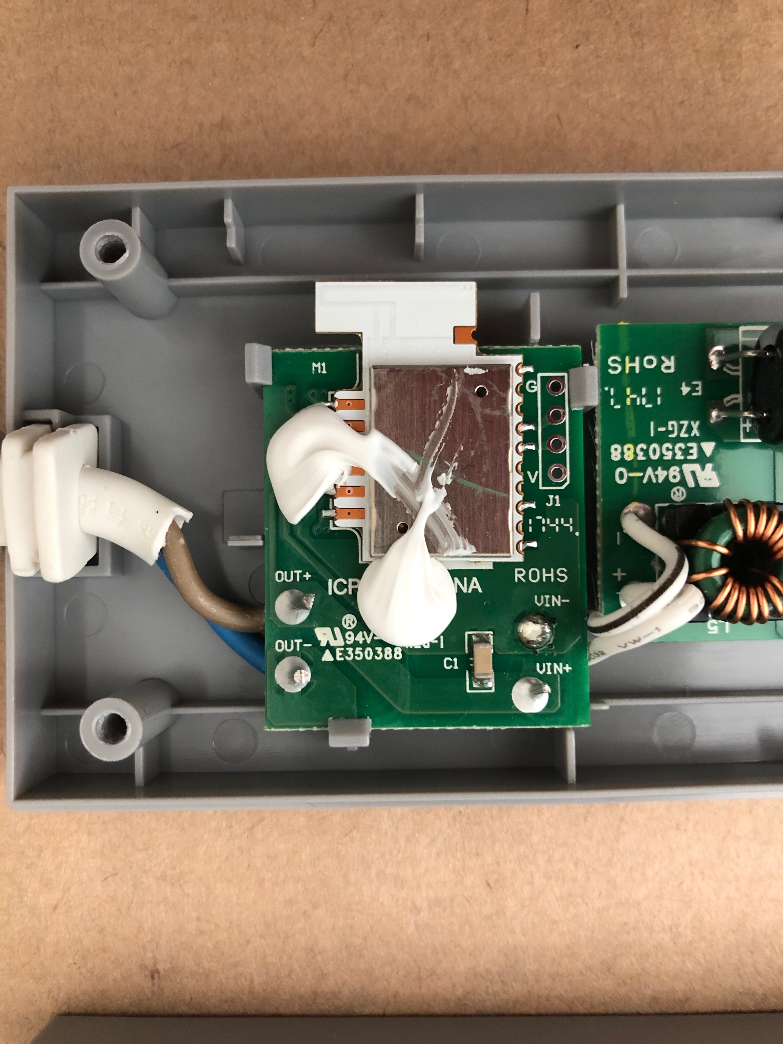
products/ICPSHC24-30EU-IL-1/images/power_control_top_01.jpg
