basilfx/TRADFRI-Hacking/products/ICPSHC24-30EU-IL-1/images/transformer_bottom_01.jpg

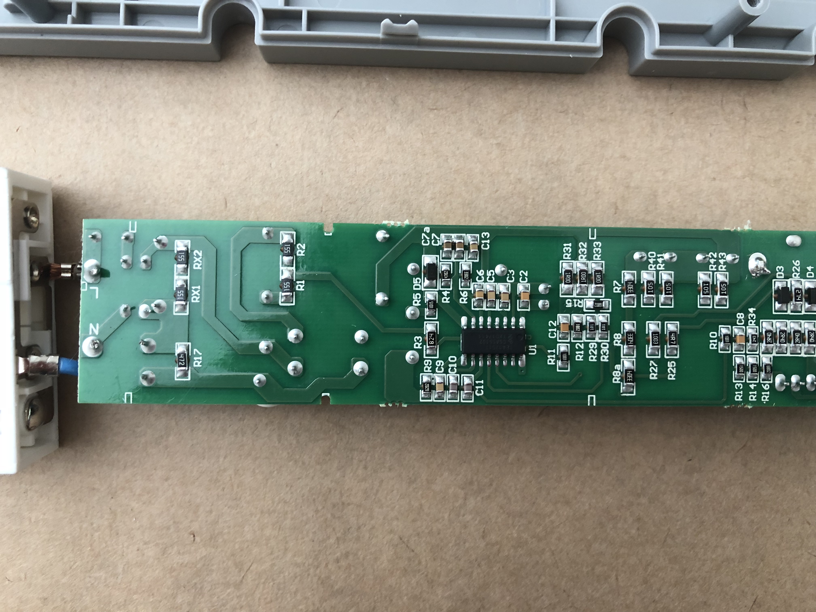
products/ICPSHC24-30EU-IL-1/images/transformer_bottom_01.jpg
