basilfx/TRADFRI-Hacking/products/ICPSLC24-10NA/images/controller_bottom_01.jpg

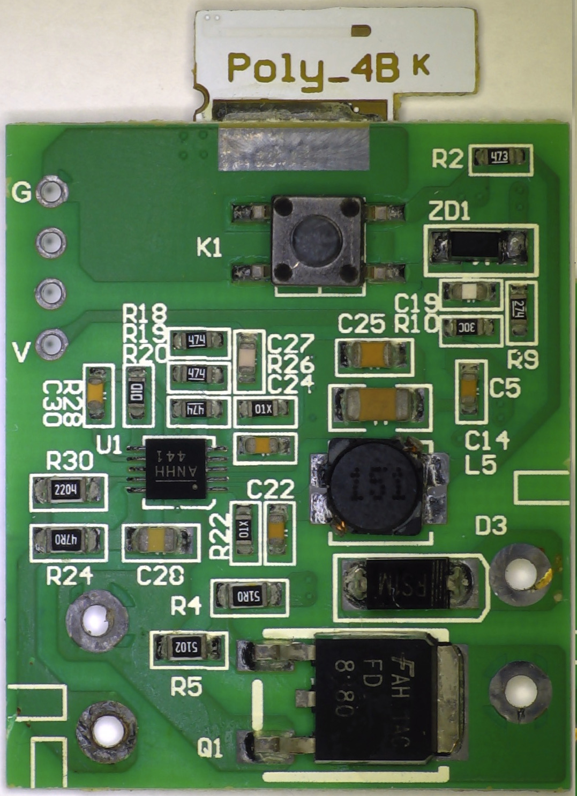
products/ICPSLC24-10NA/images/controller_bottom_01.jpg
