basilfx/TRADFRI-Hacking/products/ICPSLC24-10NA/images/controller_top_01.jpg

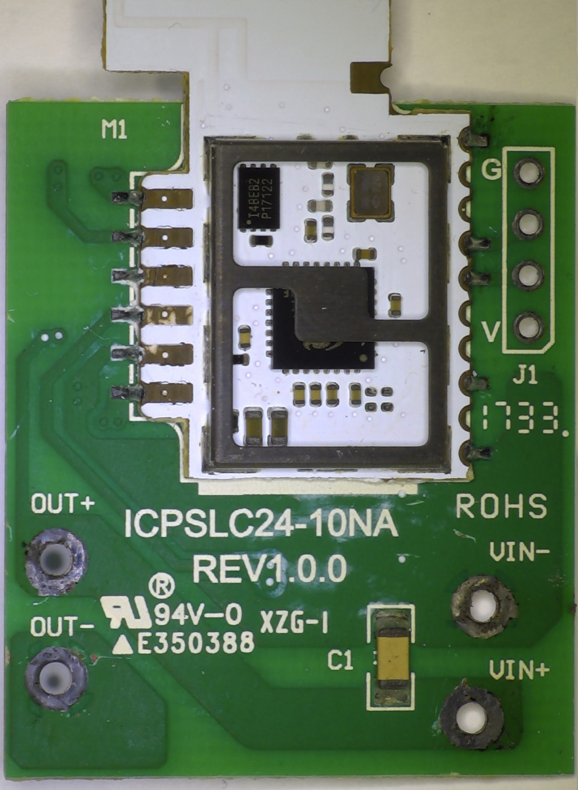
products/ICPSLC24-10NA/images/controller_top_01.jpg
