basilfx/TRADFRI-Hacking/products/ICPSLC24-10NA/images/pcb_bottom.png

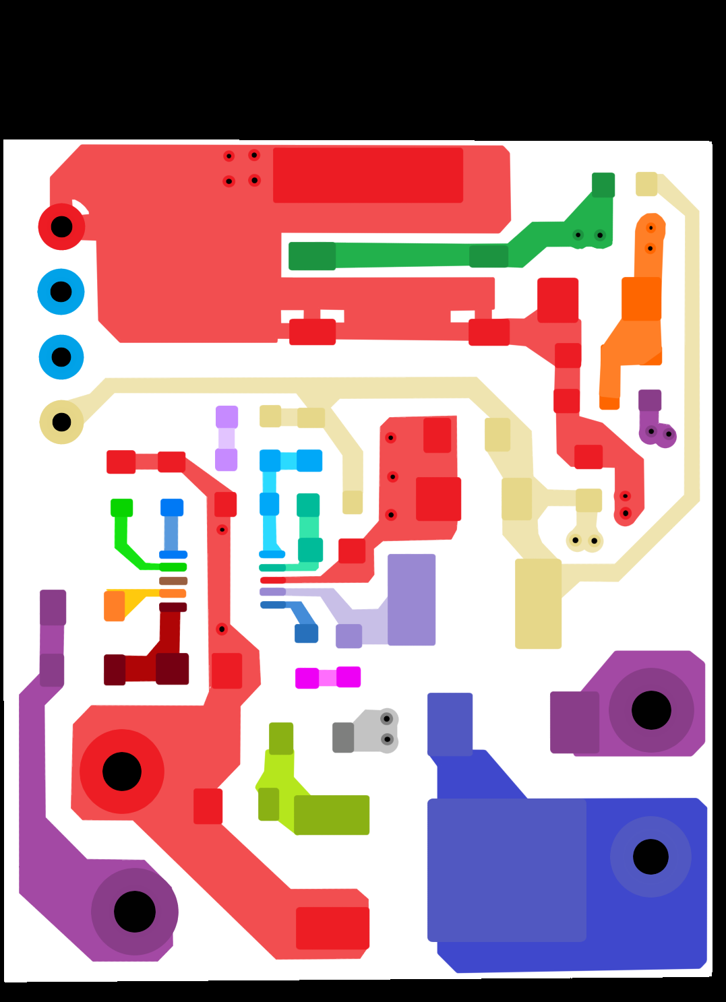
products/ICPSLC24-10NA/images/pcb_bottom.png
