basilfx/TRADFRI-Hacking/products/ICPSLC24-10NA/images/pcb_top.png

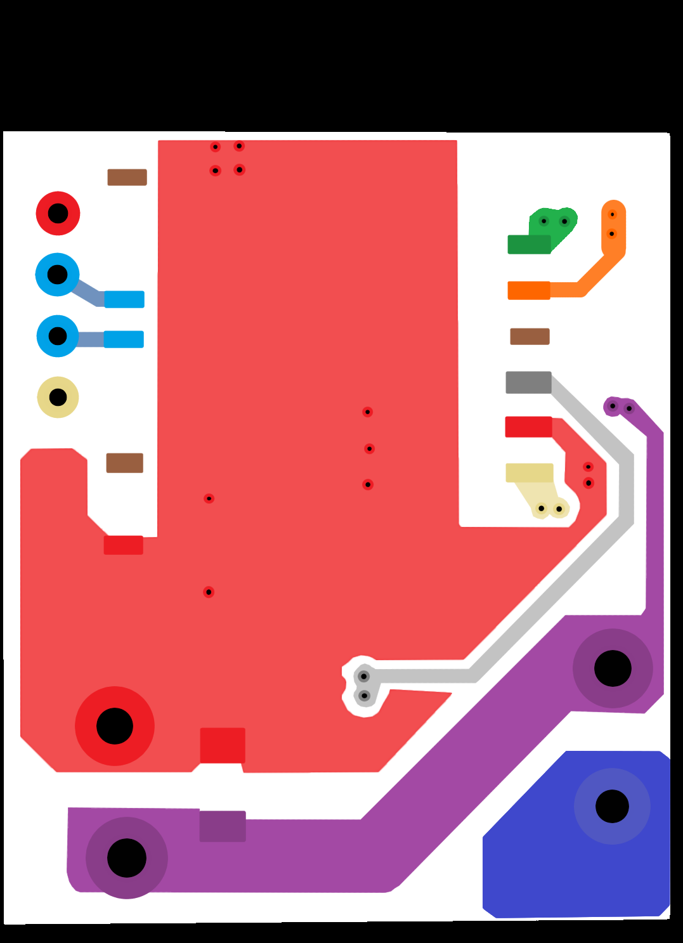
products/ICPSLC24-10NA/images/pcb_top.png
