basilfx/TRADFRI-Hacking/products/L2112/images/IMG_0796.jpeg

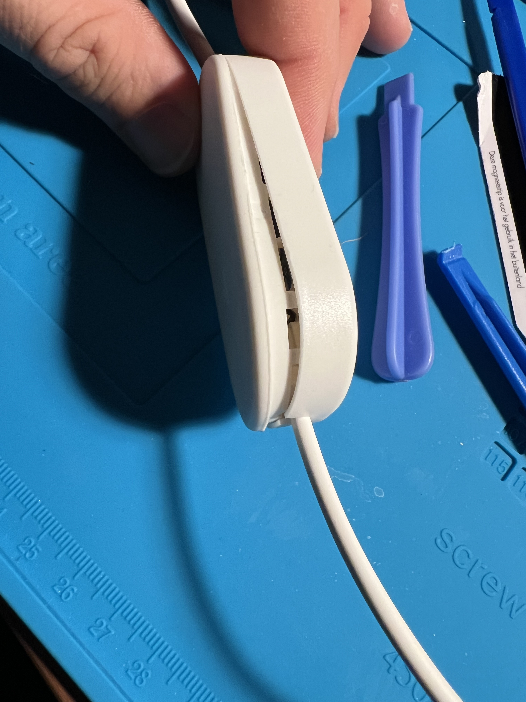
products/L2112/images/IMG_0796.jpeg
