basilfx/TRADFRI-Hacking/products/L2112/images/IMG_0797.jpeg

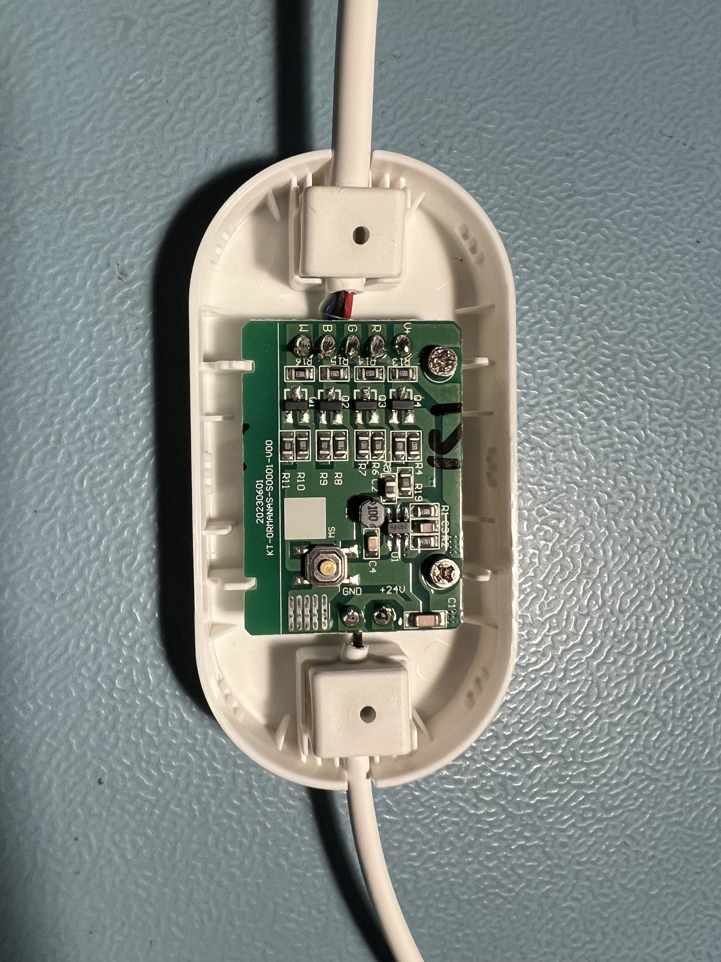
products/L2112/images/IMG_0797.jpeg
