basilfx/TRADFRI-Hacking/products/L2112/images/IMG_0798.jpeg

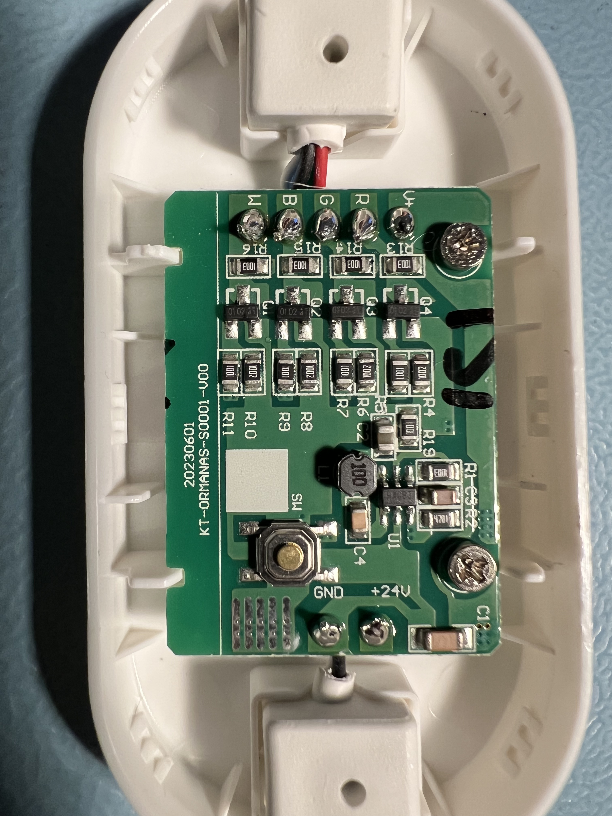
products/L2112/images/IMG_0798.jpeg
