basilfx/TRADFRI-Hacking/products/L2112/images/IMG_0799.jpeg

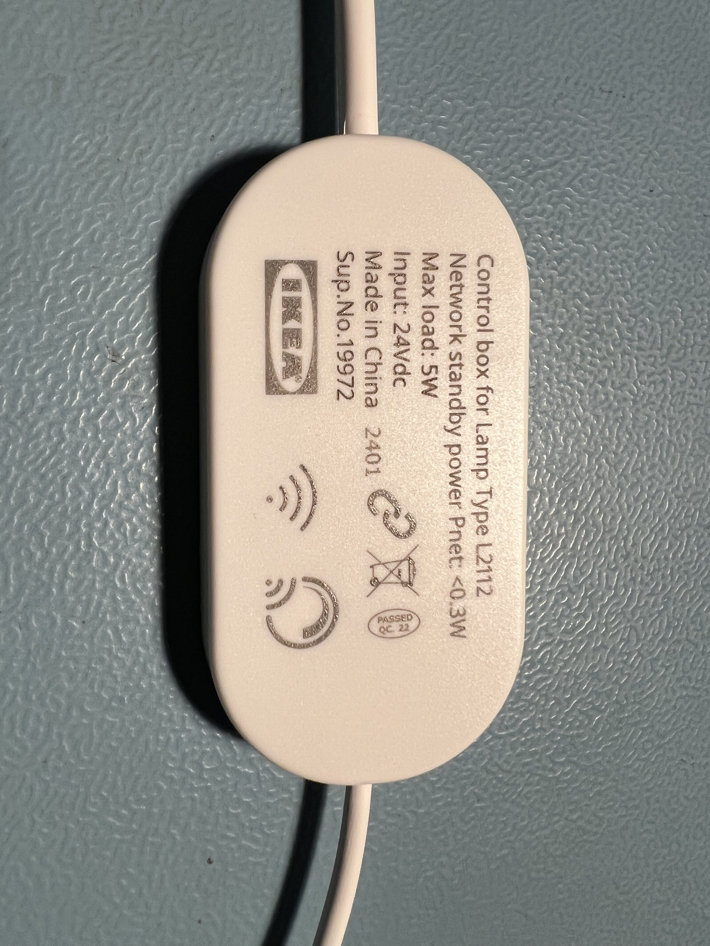
products/L2112/images/IMG_0799.jpeg
