basilfx/TRADFRI-Hacking/products/L2112/images/IMG_0800.jpeg

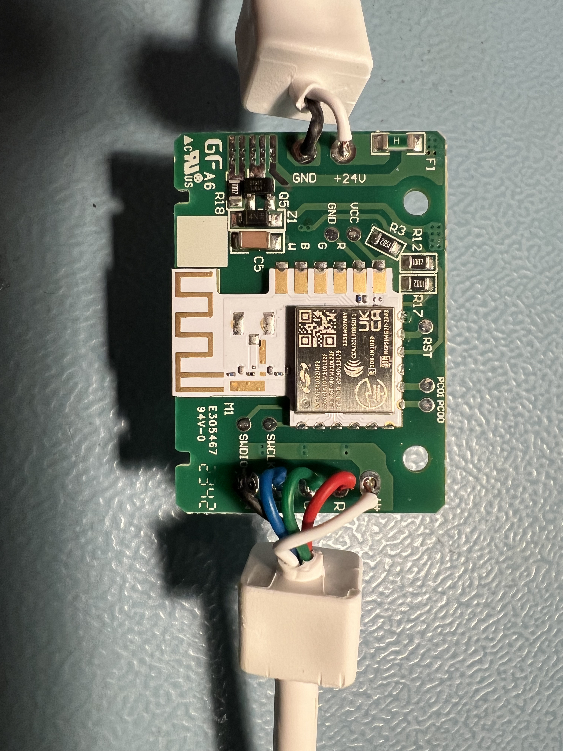
products/L2112/images/IMG_0800.jpeg
