basilfx/TRADFRI-Hacking/products/LED1537R6/images/removed-ledprint.jpg

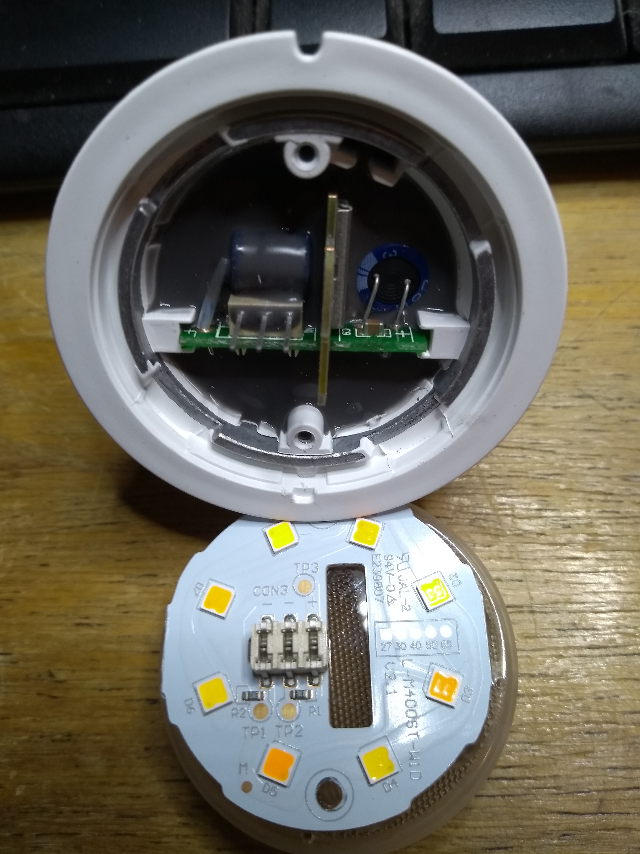
products/LED1537R6/images/removed-ledprint.jpg
