basilfx/TRADFRI-Hacking/products/LED1537R6/images/removed-potting-2.jpg

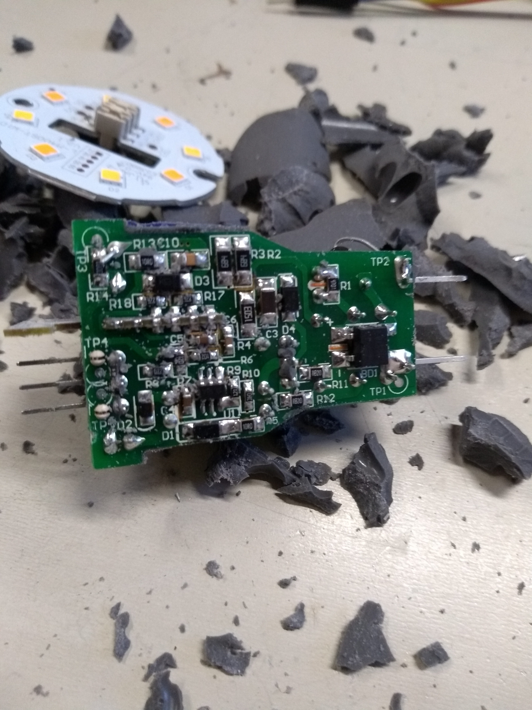
products/LED1537R6/images/removed-potting-2.jpg
