basilfx/TRADFRI-Hacking/products/LED1537R6/images/removed-potting.jpg

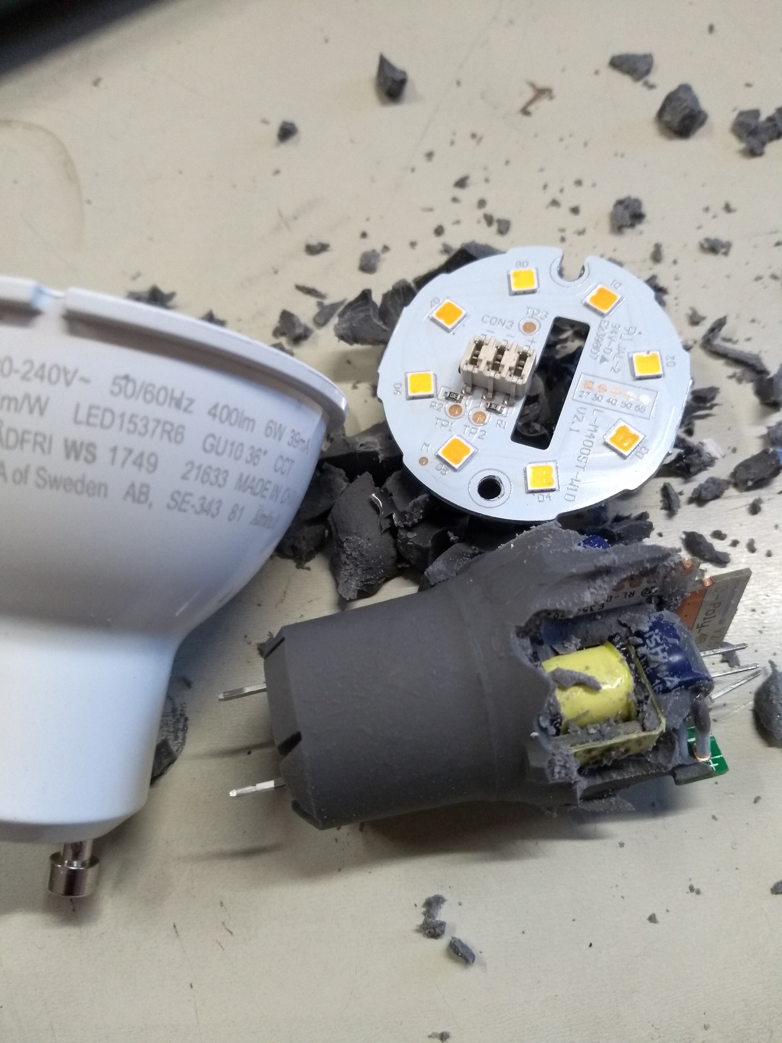
products/LED1537R6/images/removed-potting.jpg
