basilfx/TRADFRI-Hacking/products/LED1650R5/images/leds.jpg

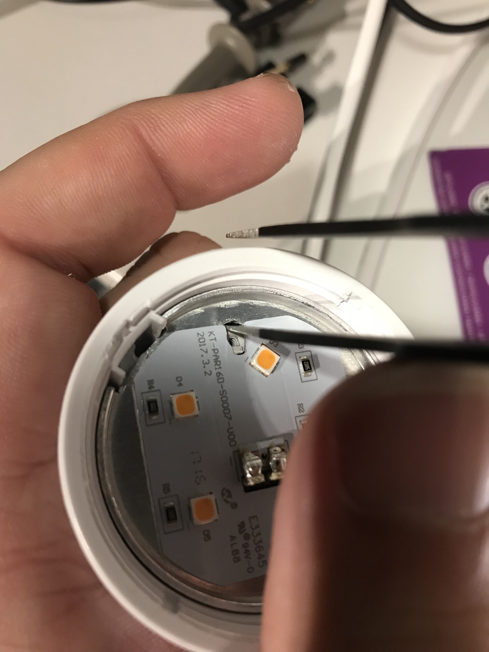
products/LED1650R5/images/leds.jpg
