basilfx/TRADFRI-Hacking/products/LED1650R5/images/lens.jpg

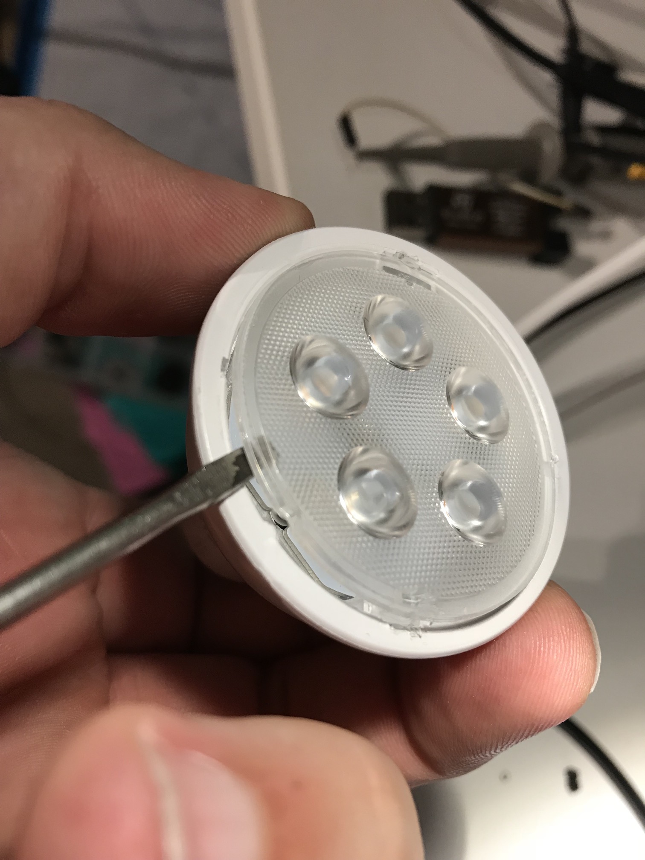
products/LED1650R5/images/lens.jpg
