basilfx/TRADFRI-Hacking/products/LED1650R5/images/lid.jpeg

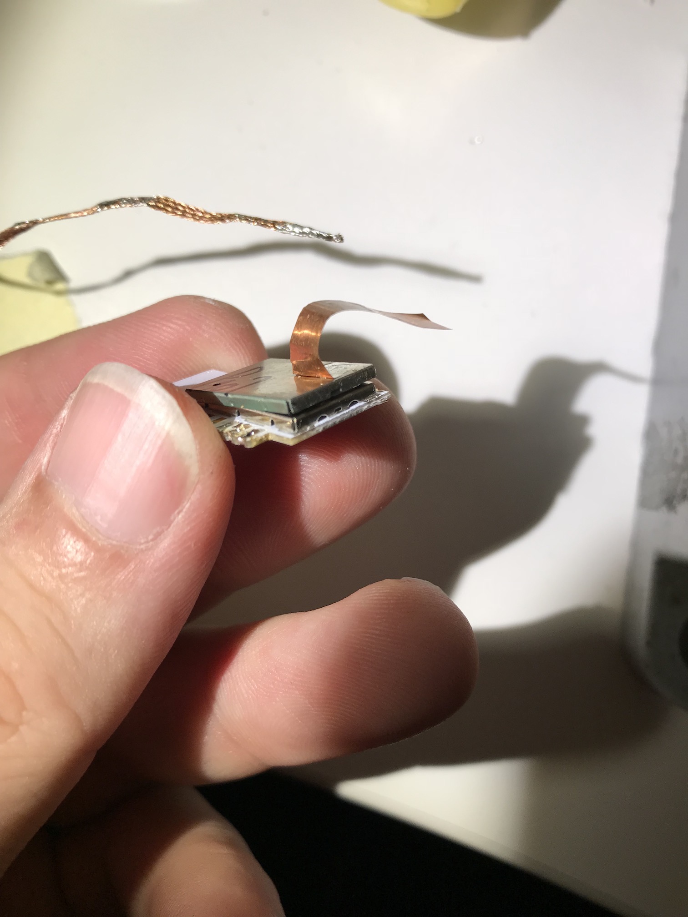
products/LED1650R5/images/lid.jpeg
