basilfx/TRADFRI-Hacking/products/LED1650R5/images/psu.jpg

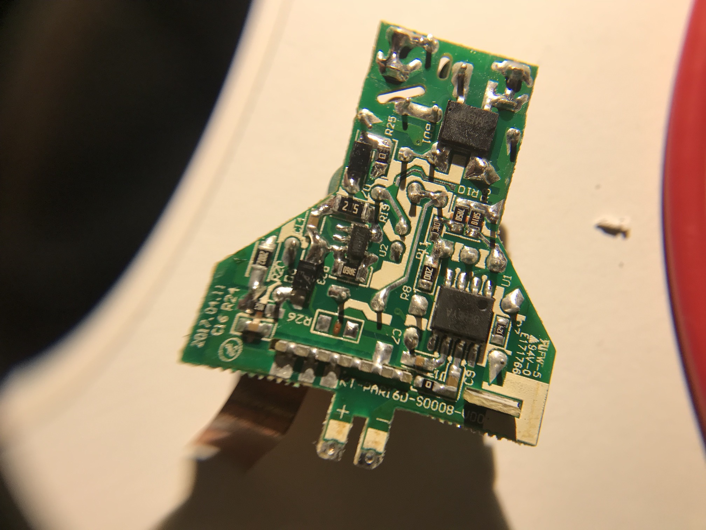
products/LED1650R5/images/psu.jpg
