basilfx/TRADFRI-Hacking/products/LED1837R5/firmwares/2.1.022/binvis.png

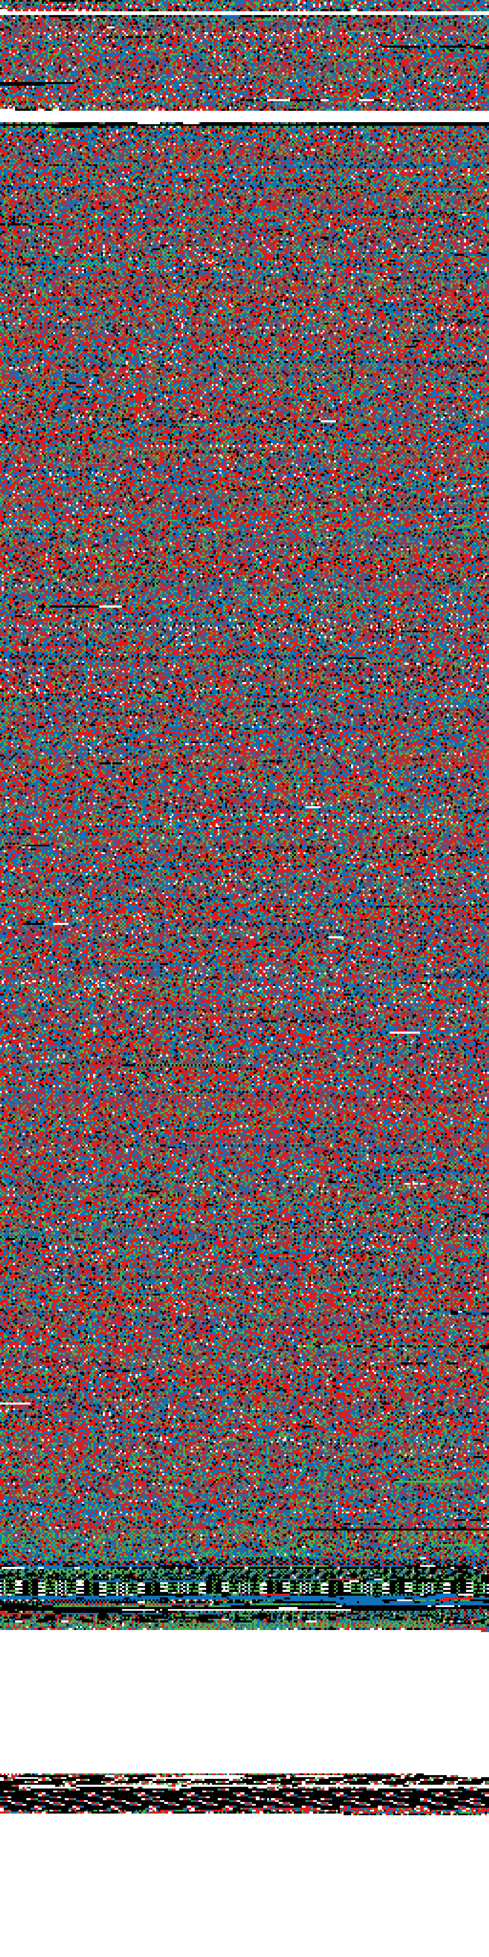
products/LED1837R5/firmwares/2.1.022/binvis.png
