basilfx/TRADFRI-Hacking/products/LED1837R5/images/leds.jpg

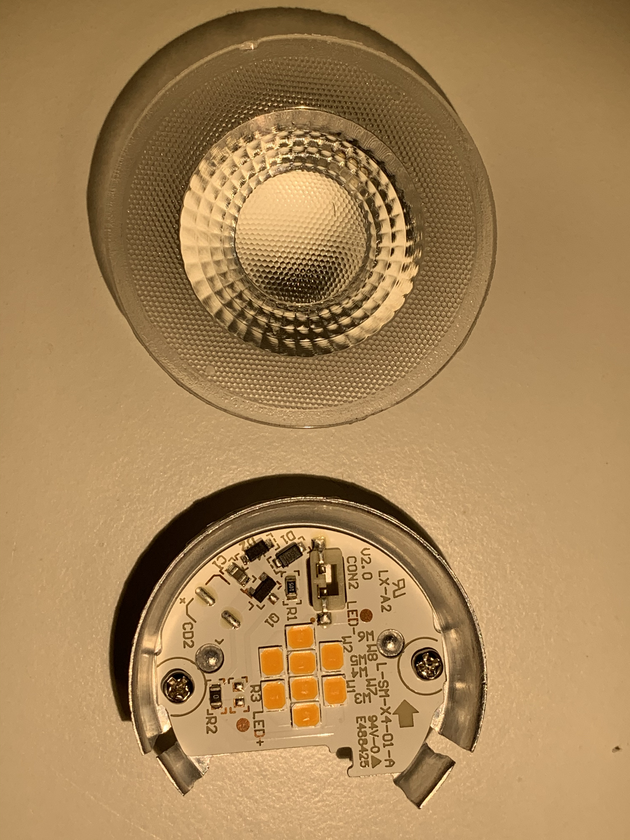
products/LED1837R5/images/leds.jpg
