basilfx/TRADFRI-Hacking/products/LED1837R5/images/lens_removed.jpg

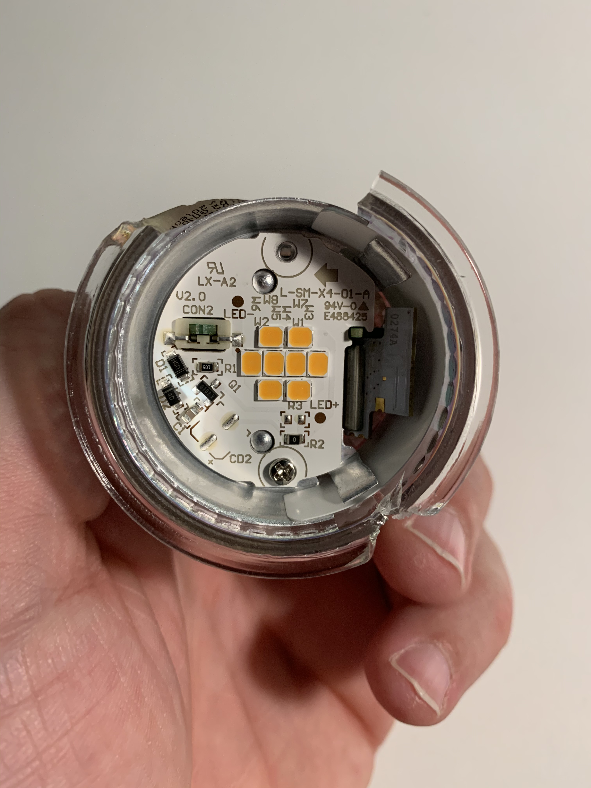
products/LED1837R5/images/lens_removed.jpg
