basilfx/TRADFRI-Hacking/products/LED1837R5/images/module.jpg

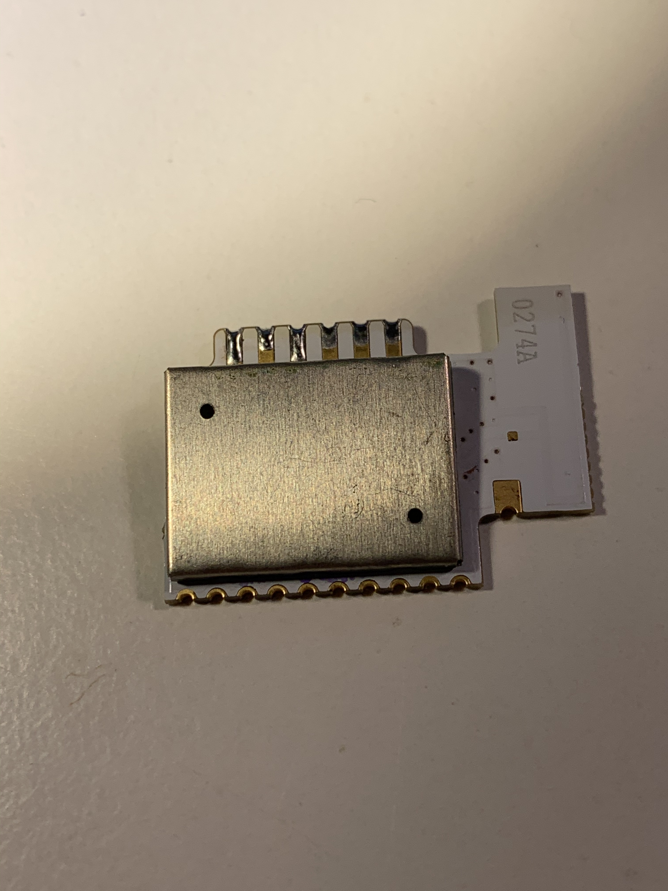
products/LED1837R5/images/module.jpg
