basilfx/TRADFRI-Hacking/products/LED1837R5/images/opened.jpg

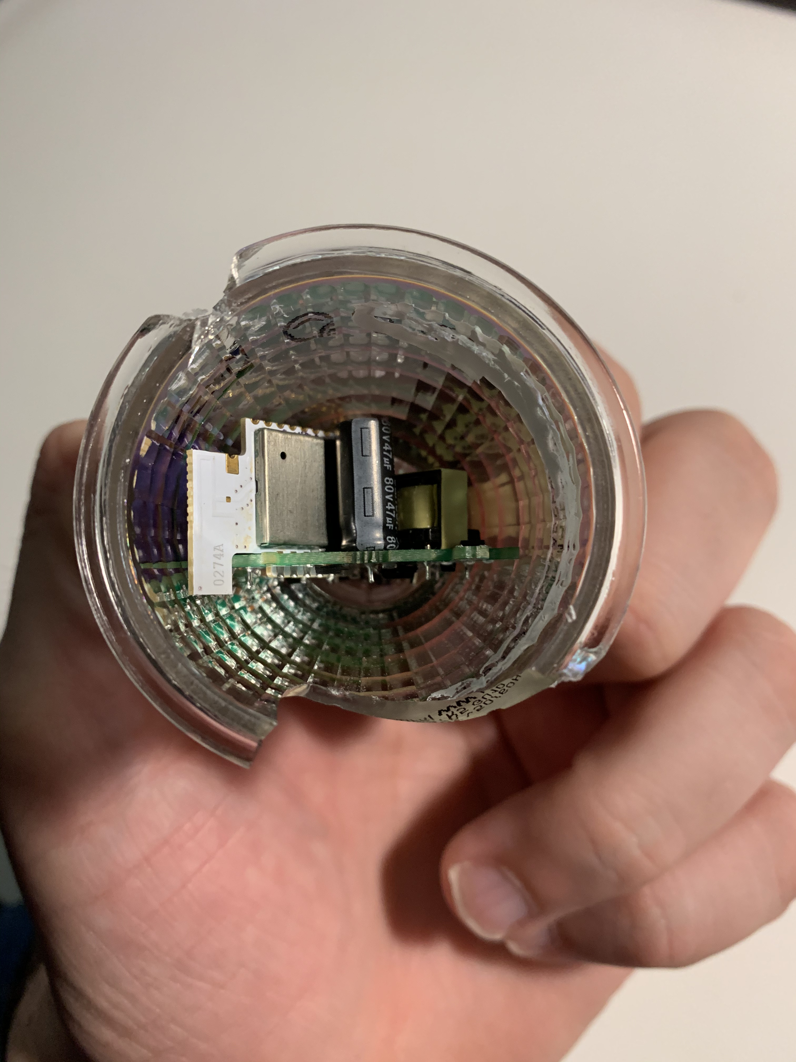
products/LED1837R5/images/opened.jpg
