basilfx/TRADFRI-Hacking/products/LED1837R5/images/psu2.jpg

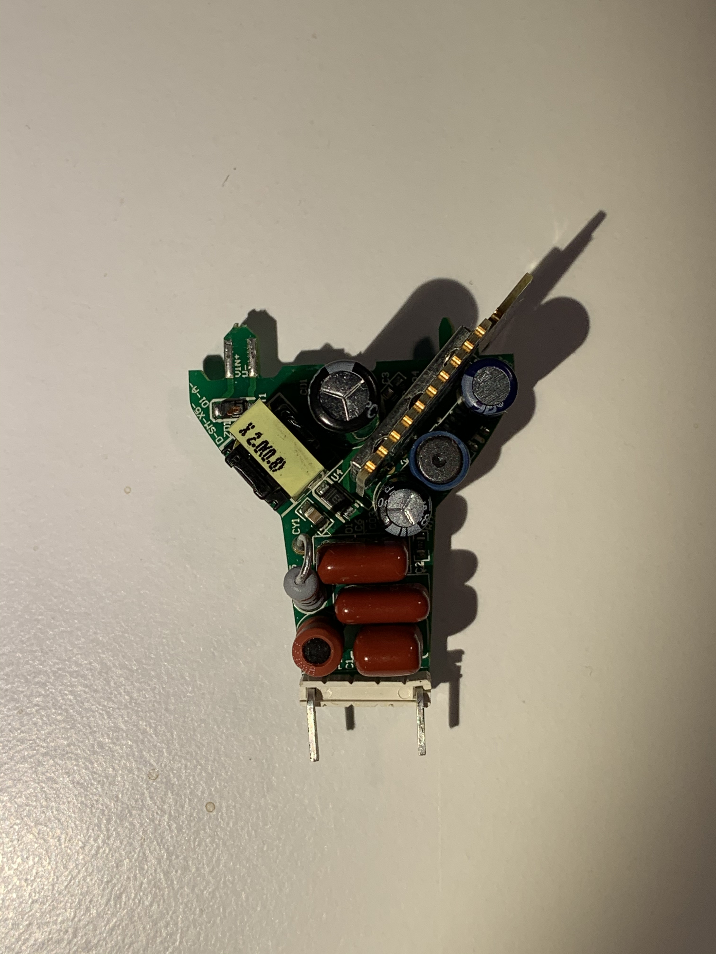
products/LED1837R5/images/psu2.jpg
