basilfx/TRADFRI-Hacking/products/LED1837R5/images/psu.jpg

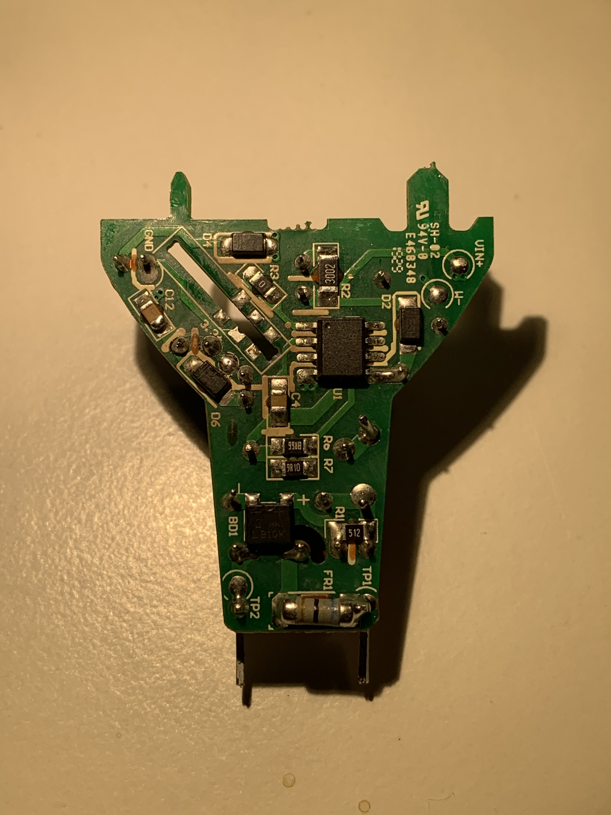
products/LED1837R5/images/psu.jpg
