basilfx/TRADFRI-Hacking/products/E2013/analysis/DS1Z_QuickPrint4.png

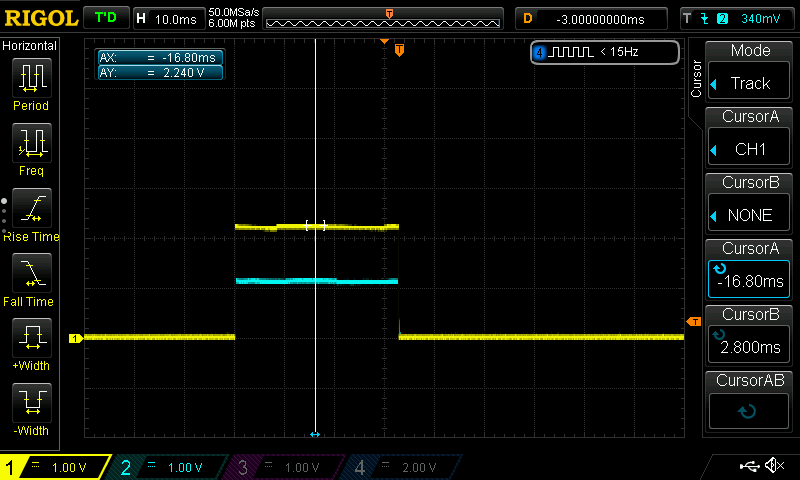
products/E2013/analysis/DS1Z_QuickPrint4.png
