basilfx/TRADFRI-Hacking/products/LED1537R6/images/led-print.jpg

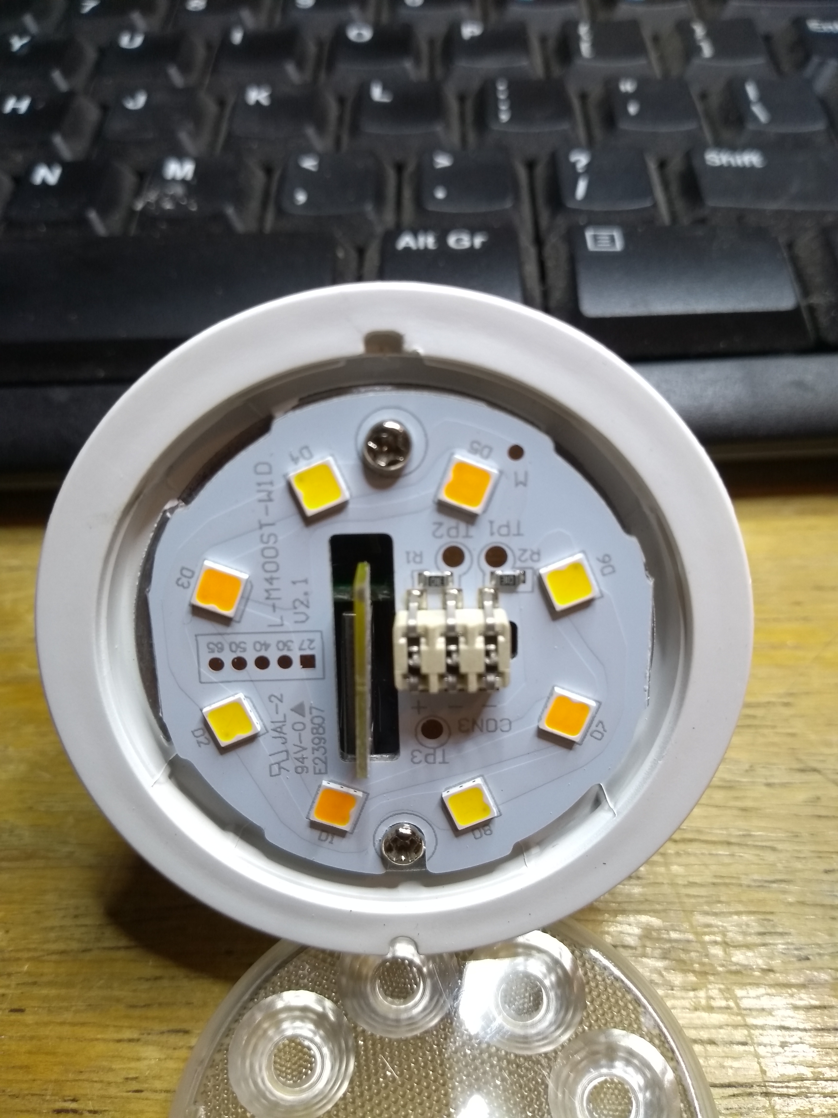
products/LED1537R6/images/led-print.jpg
